kholia/HF-PA-v4/HF-PA-Simulations/5Vpp @ 5v @ 21 MHz.png

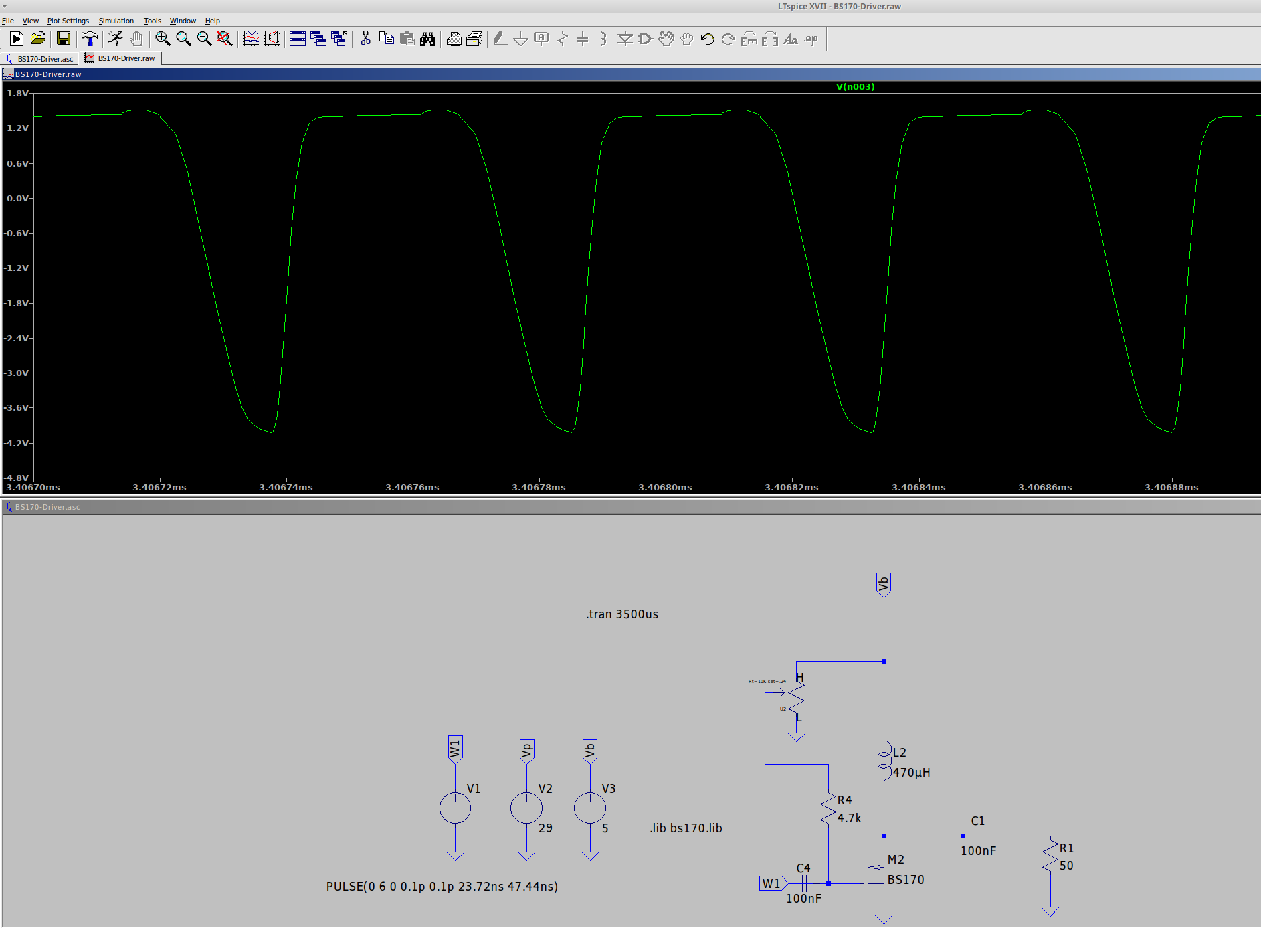
HF-PA-Simulations/5Vpp @ 5v @ 21 MHz.png
