kholia/HF-PA-v4/HF-PA-Simulations/8Vpp @ 5v.png

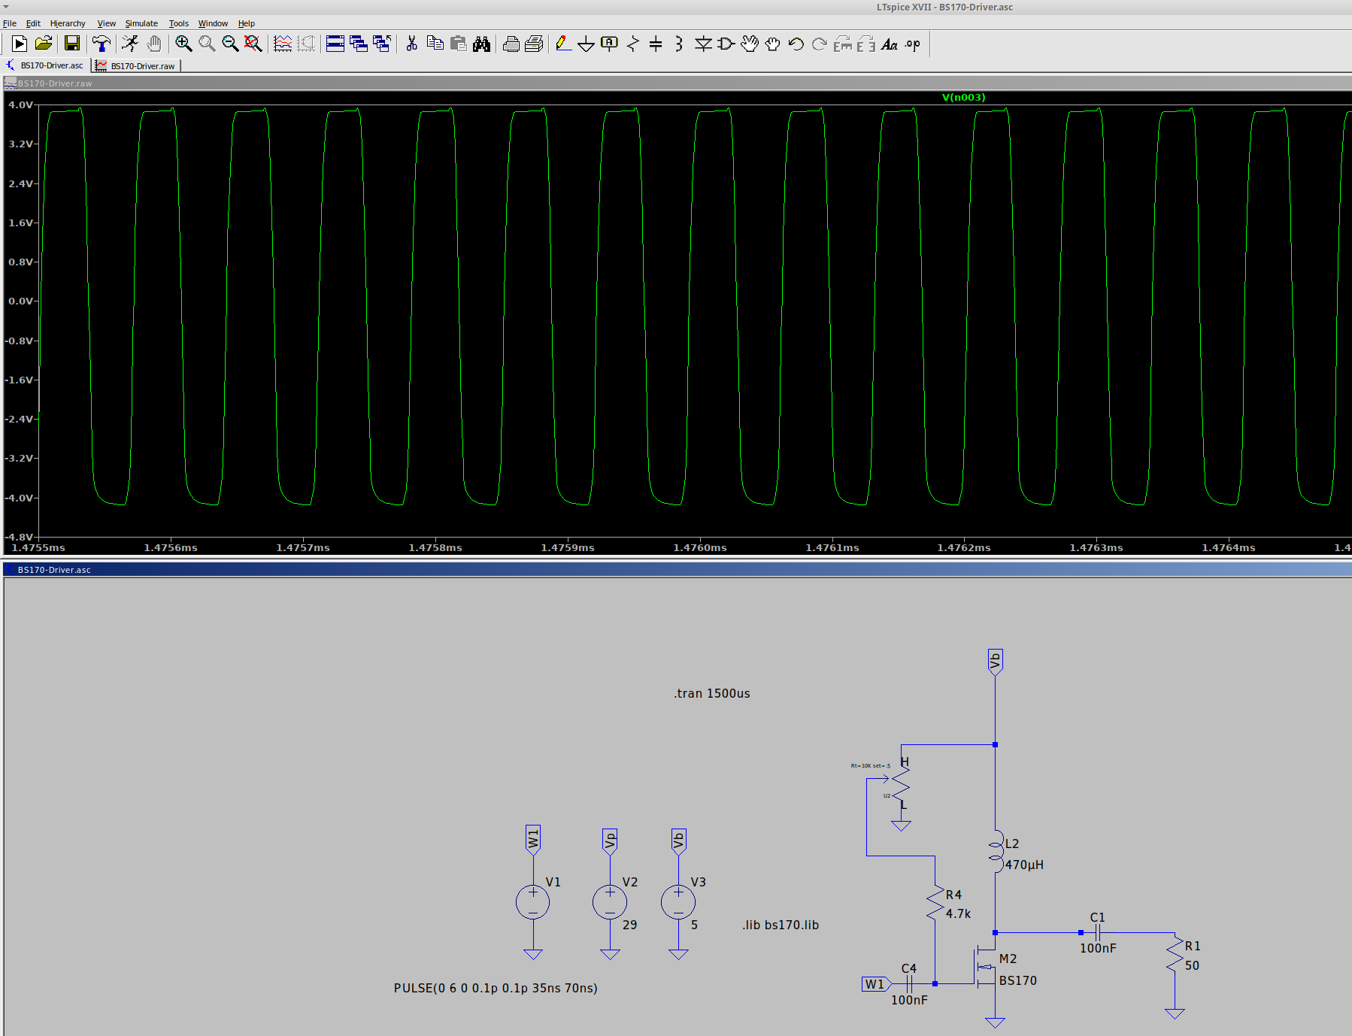
HF-PA-Simulations/8Vpp @ 5v.png
