kholia/HF-PA-v4/HF-PA-Simulations/11Vpp @ 9v @ 21 MHz.png

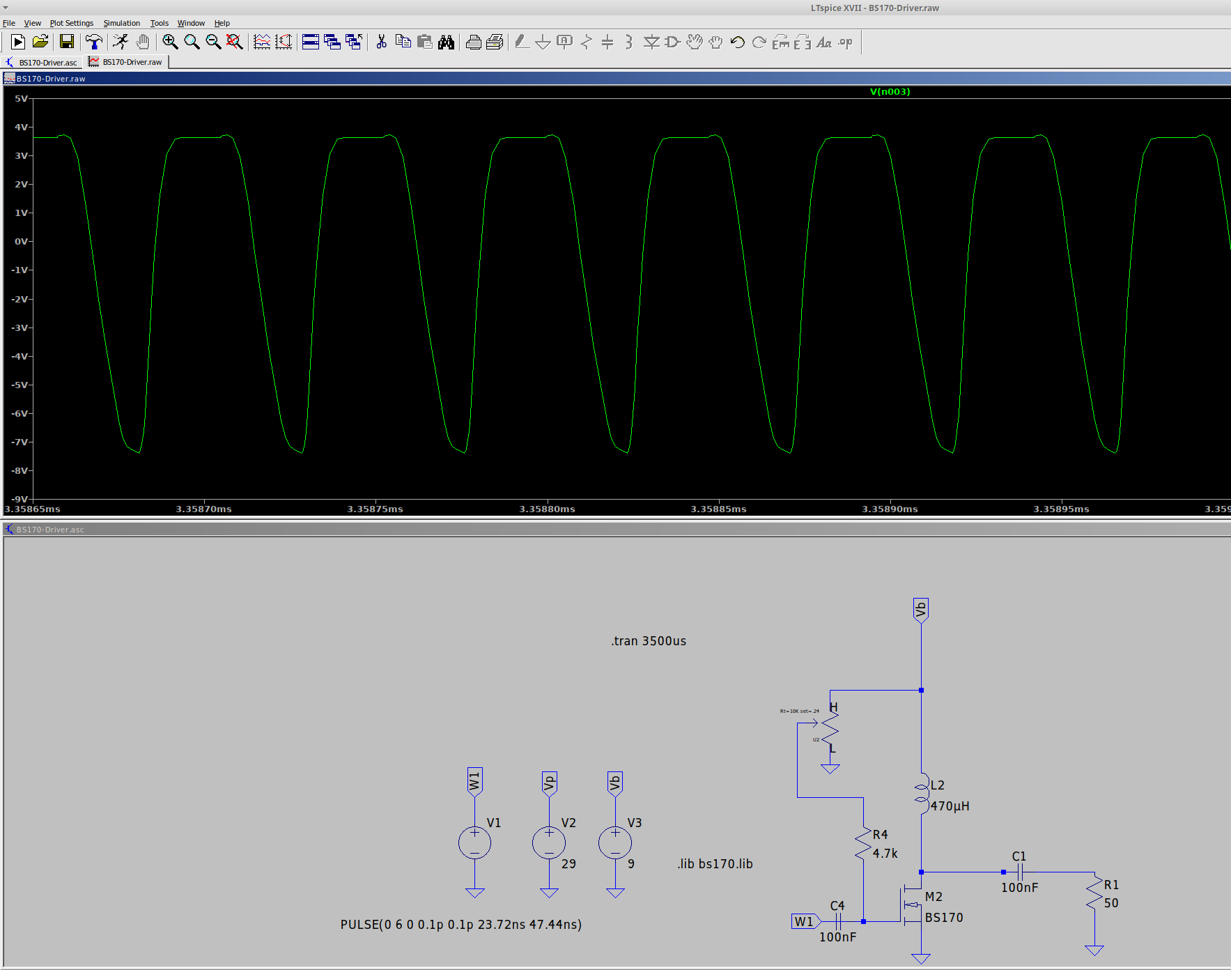
HF-PA-Simulations/11Vpp @ 9v @ 21 MHz.png
