kholia/HF-PA-v4/HF-PA-Simulations/12Vpp @ 9v.png

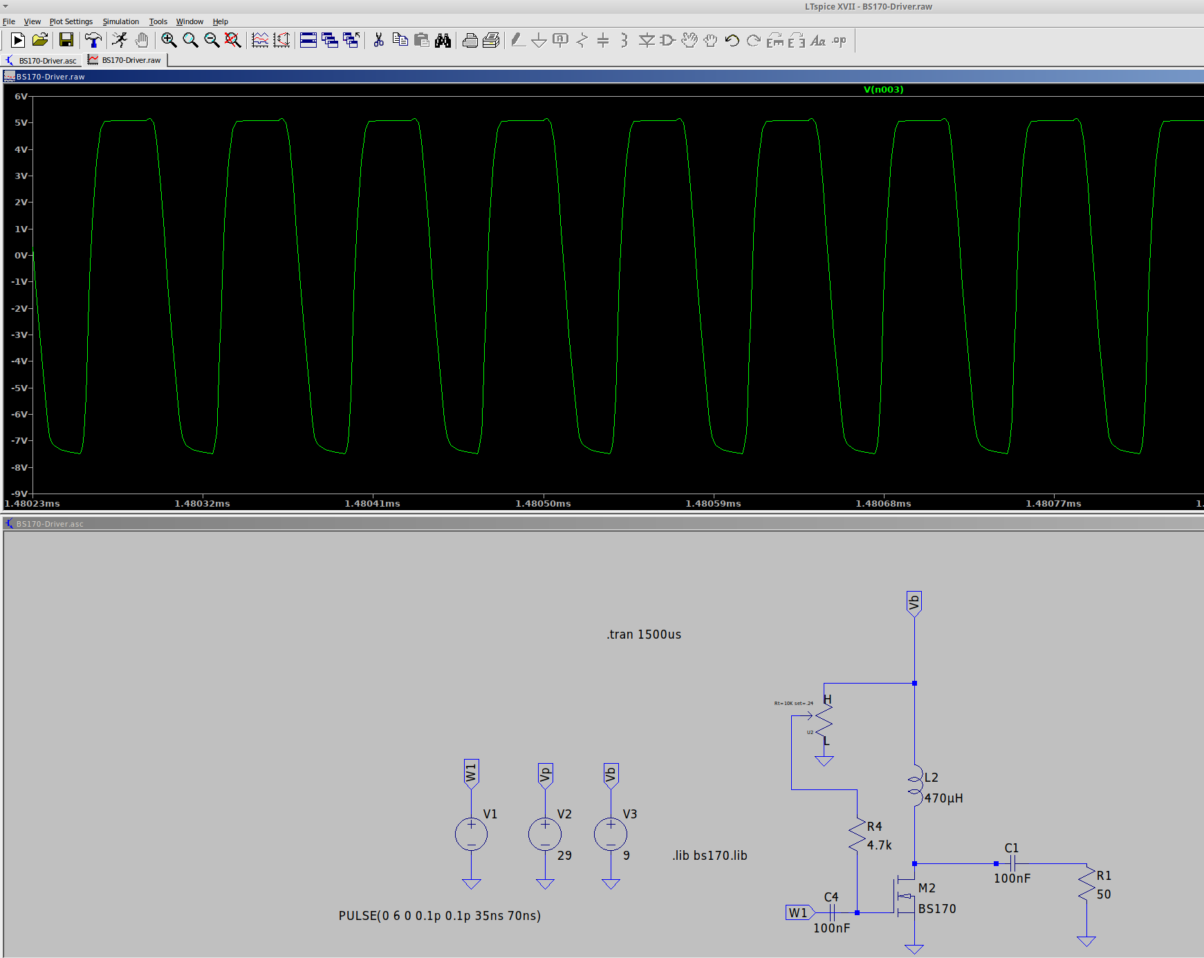
HF-PA-Simulations/12Vpp @ 9v.png
