kholia/HF-PA-v4/HF-PA-Simulations/12Vpp @ 12v @ 21 MHz (Actual Si5351 Drive).png

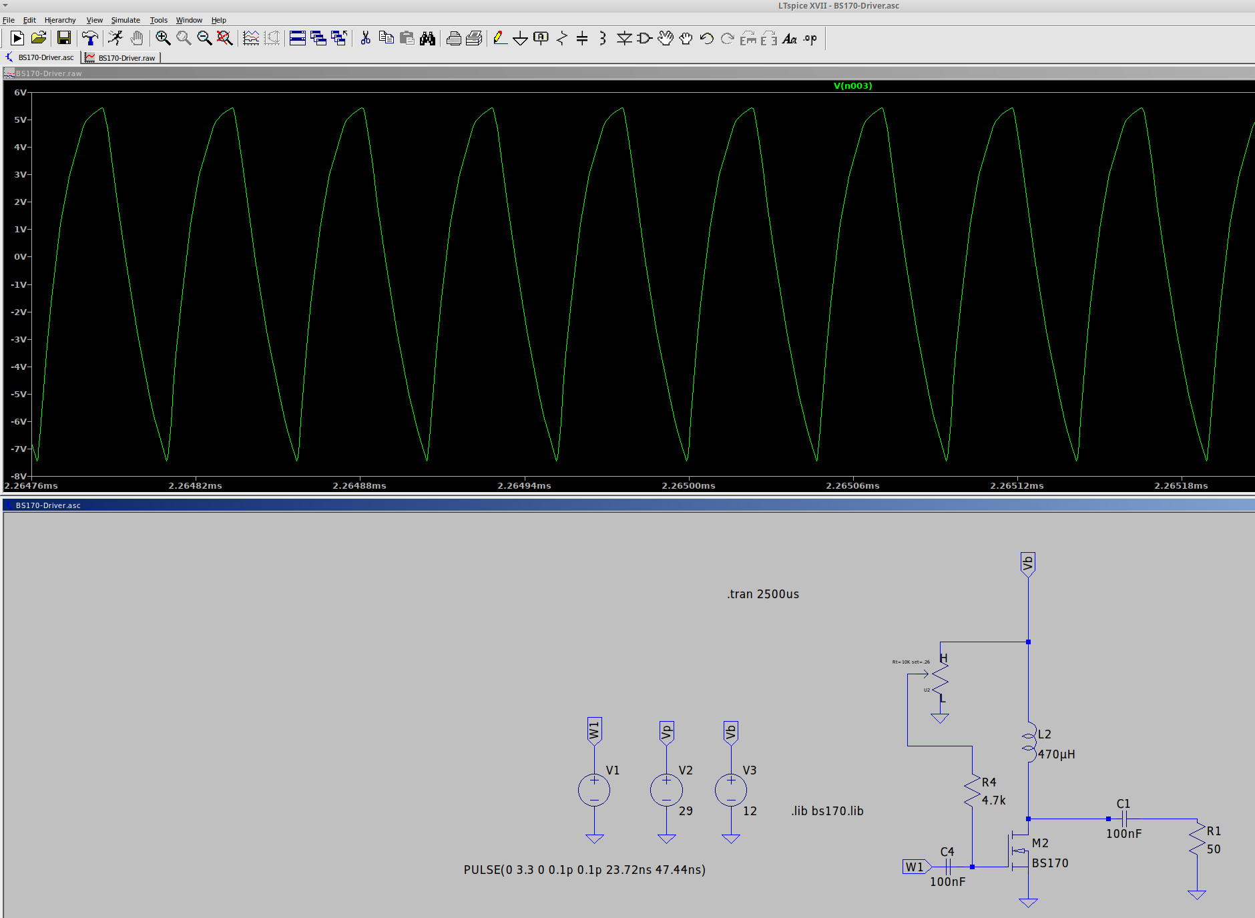
HF-PA-Simulations/12Vpp @ 12v @ 21 MHz (Actual Si5351 Drive).png
