kholia/HF-PA-v4/HF-PA-Simulations/17Vpp @ 12v @ 21 MHz.png

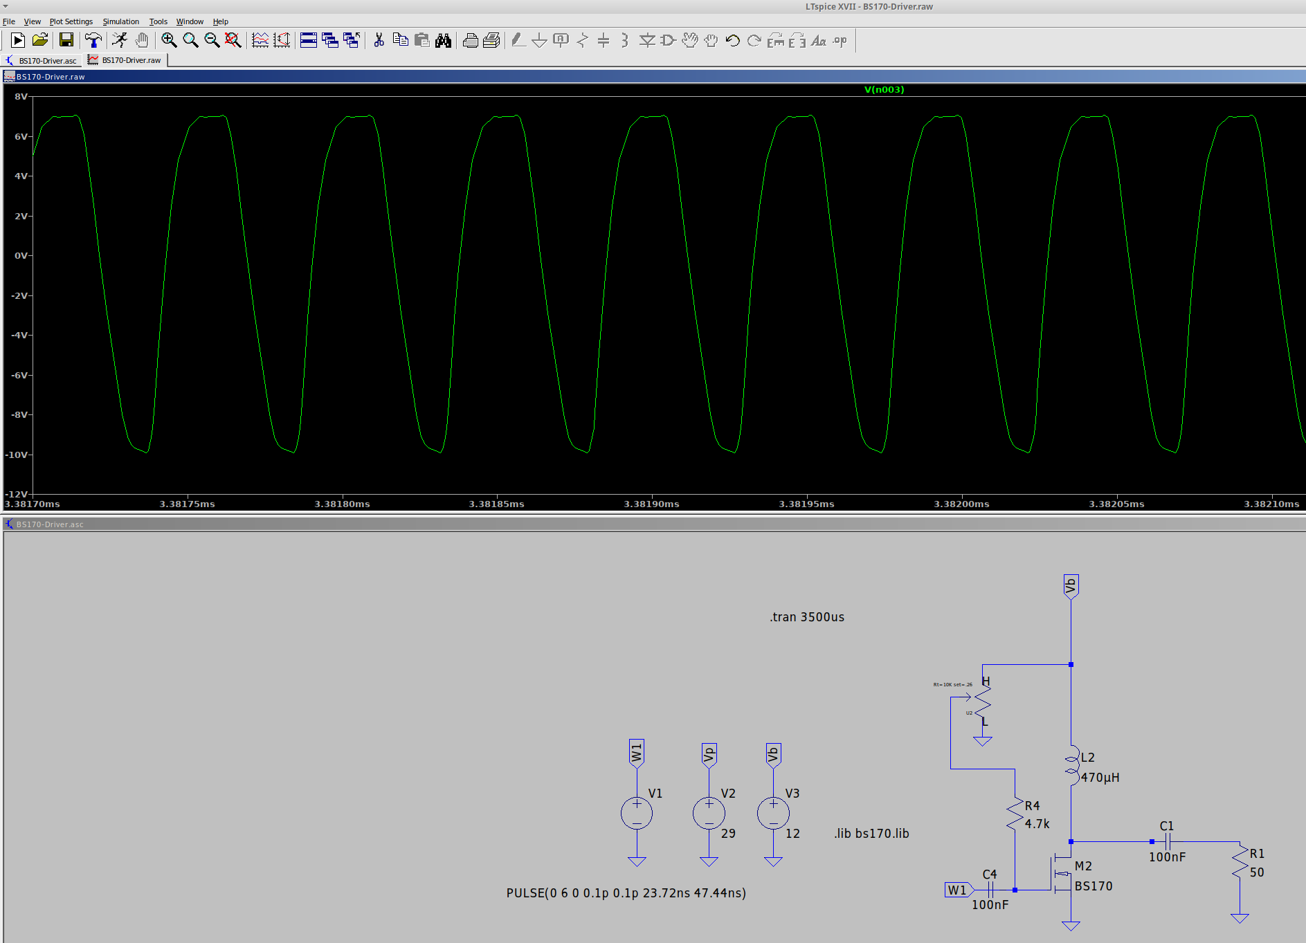
HF-PA-Simulations/17Vpp @ 12v @ 21 MHz.png
