kholia/HF-PA-v4/HF-PA-Simulations/DS1054Z_DS1ZA203916662_2021-10-18_14.36.06.png

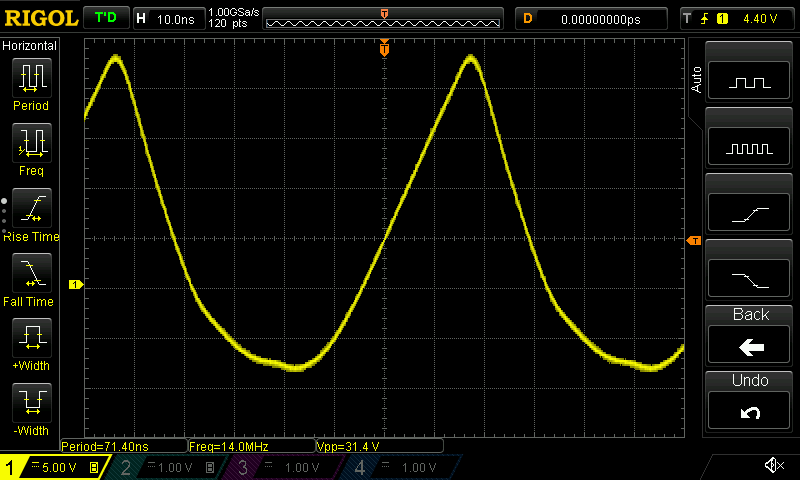
HF-PA-Simulations/DS1054Z_DS1ZA203916662_2021-10-18_14.36.06.png
