kholia/HF-PA-v4/HF-PA-Simulations/Screenshot_2021-10-14_11-42-27.png

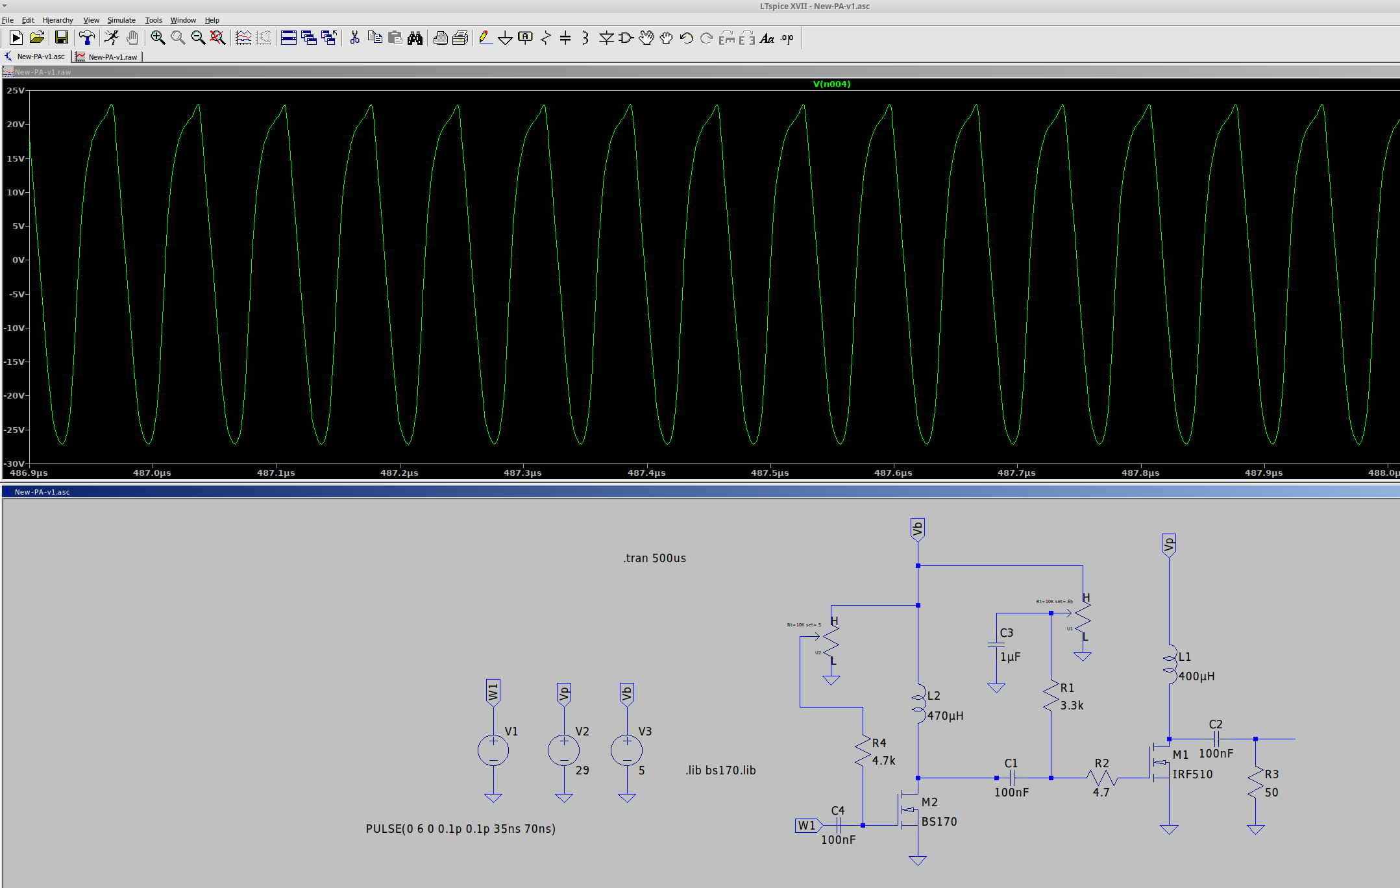
HF-PA-Simulations/Screenshot_2021-10-14_11-42-27.png
