kholia/HF-PA-v4/Info/25wlinear-small.png

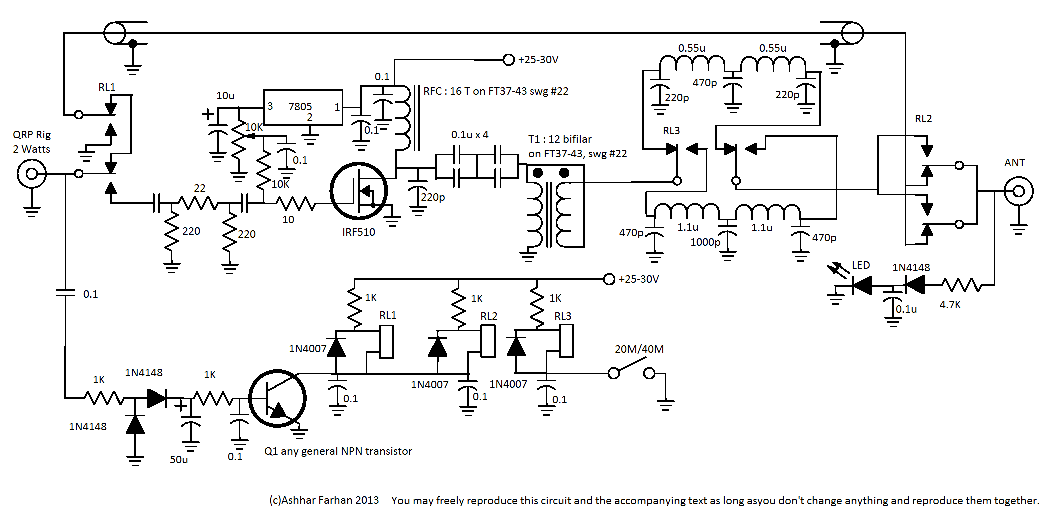
Info/25wlinear-small.png
