kholia/HF-PA-v4/Info/100nF 100V Non-Polar Polyester Film Capacitor - Philips.jpg

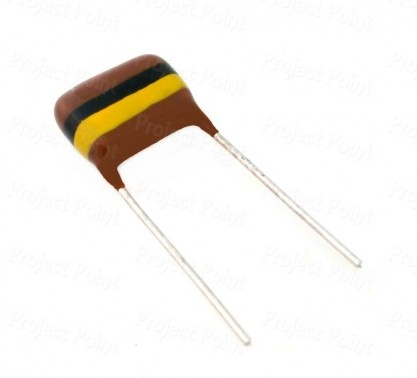
Info/100nF 100V Non-Polar Polyester Film Capacitor - Philips.jpg
