kholia/HF-PA-v4/Info/(220)_ZX-SSB_II_PA.png

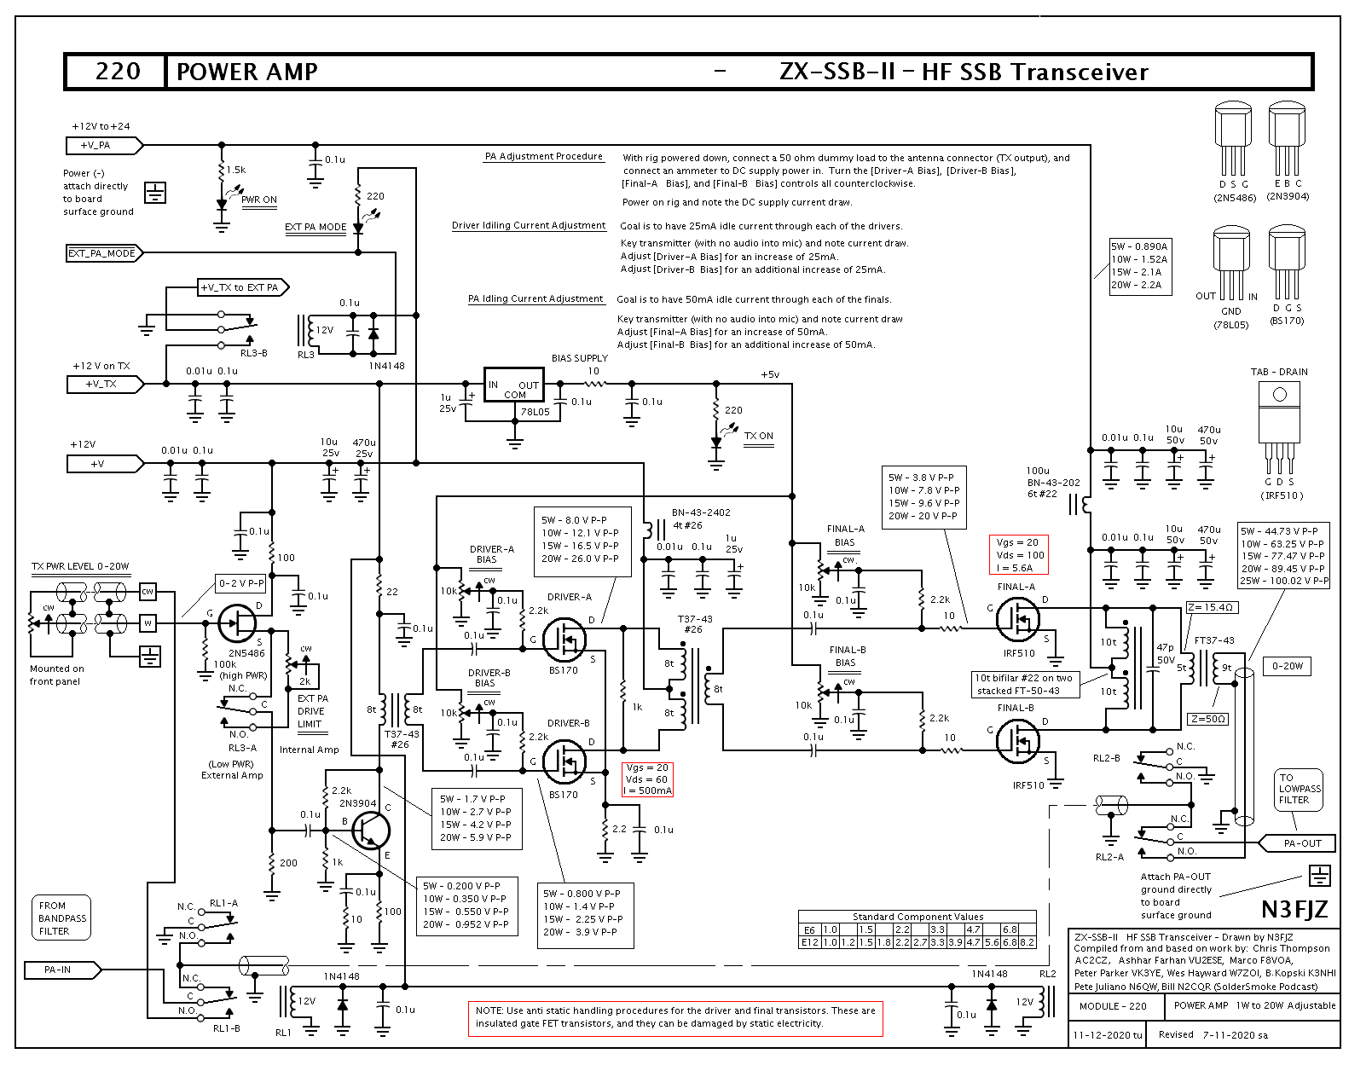
Info/(220)_ZX-SSB_II_PA.png
