kholia/HF-PA-v4/Info/Fake 7805 CV - Mar 2018.jpeg

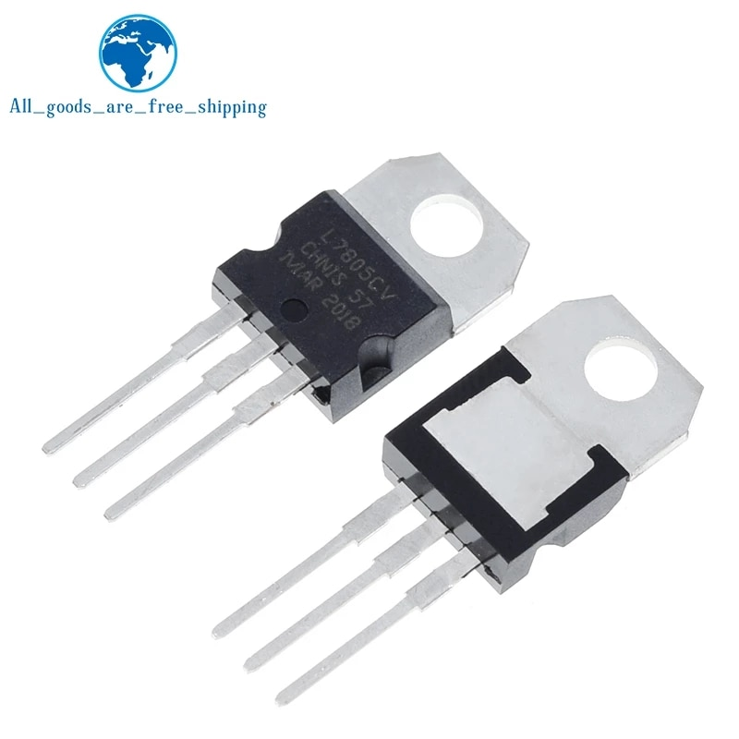
Info/Fake 7805 CV - Mar 2018.jpeg
