kholia/HF-PA-v4/Info/Fake ST 7805.jpg

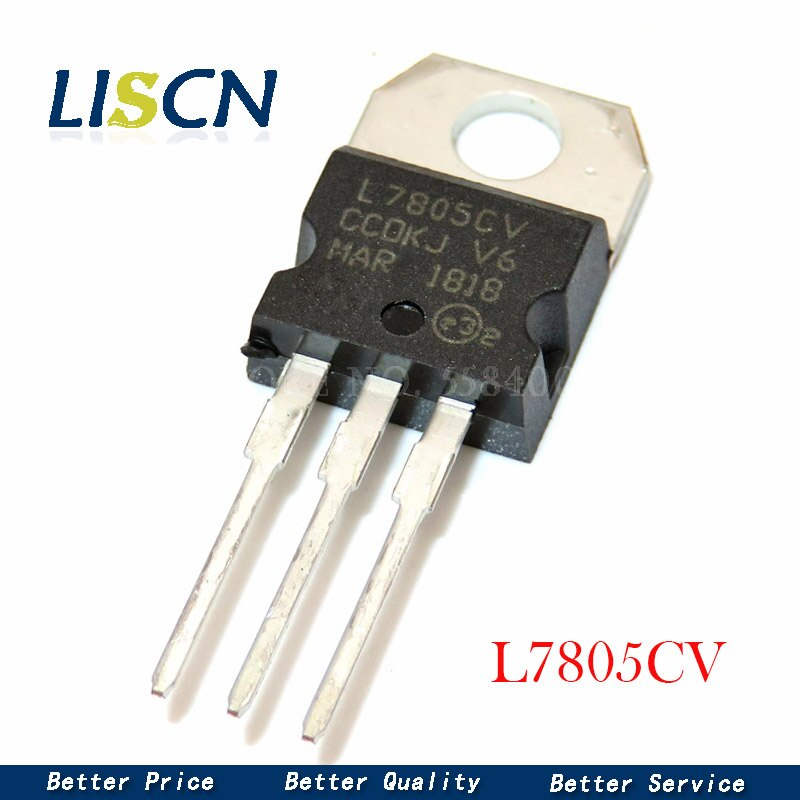
Info/Fake ST 7805.jpg
