kholia/HF-PA-v4/Info/Fake ST 7805.webp

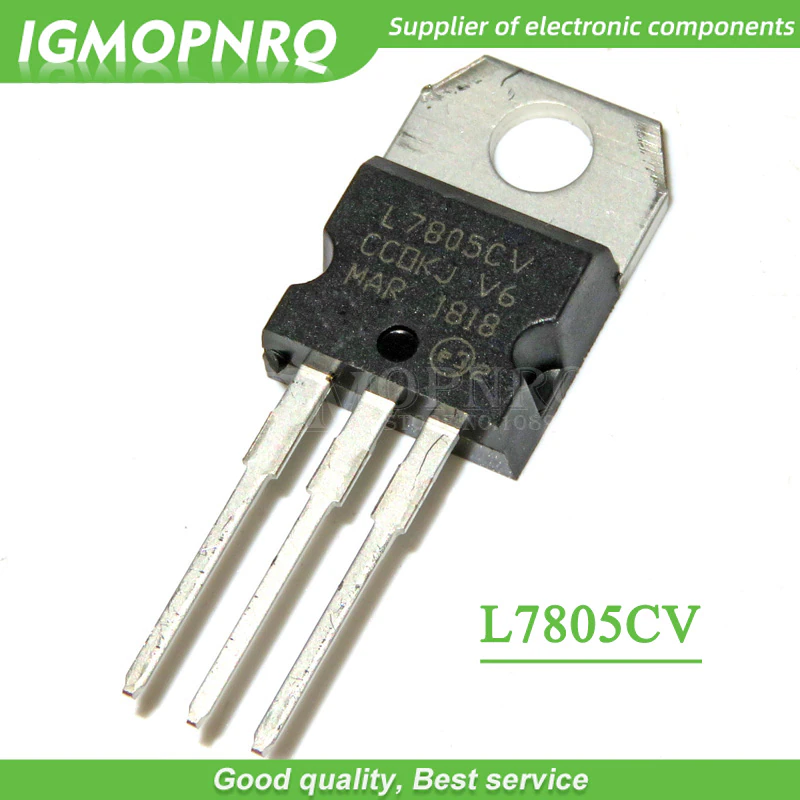
Info/Fake ST 7805.webp
