kholia/HF-PA-v4/Info/Heatsink TO-220.jpg

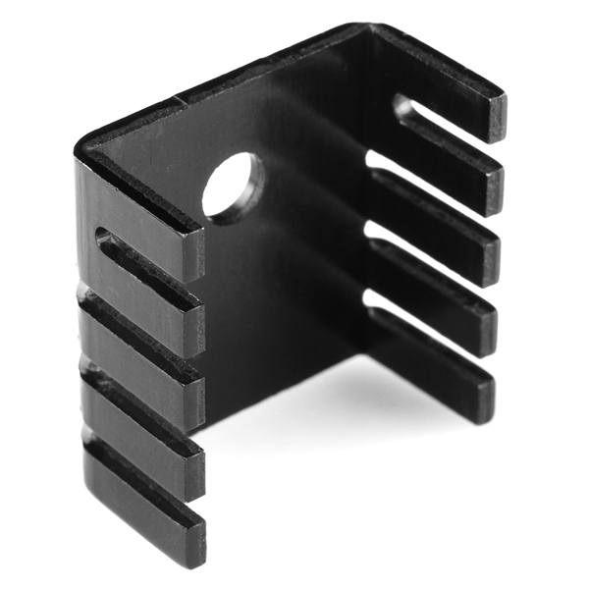
Info/Heatsink TO-220.jpg
