kholia/HF-PA-v4/Info/Hot mashup idea - was found independently on TG first.png

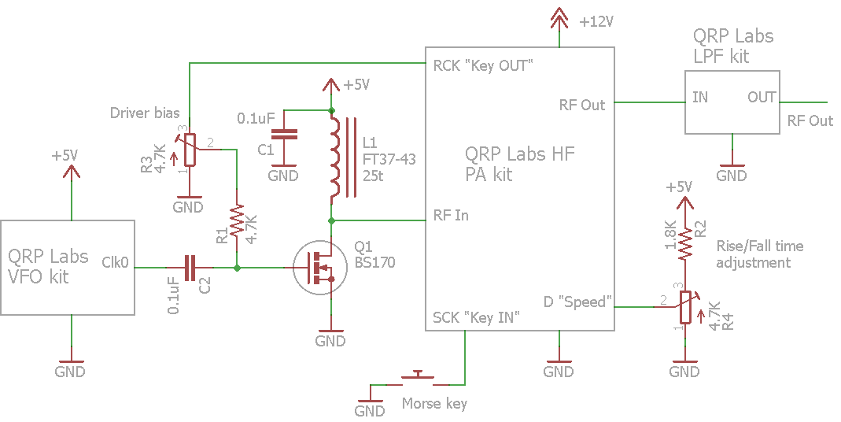
Info/Hot mashup idea - was found independently on TG first.png
