kholia/HF-PA-v4/Info/IRF530-SEC-TO-220.jpg

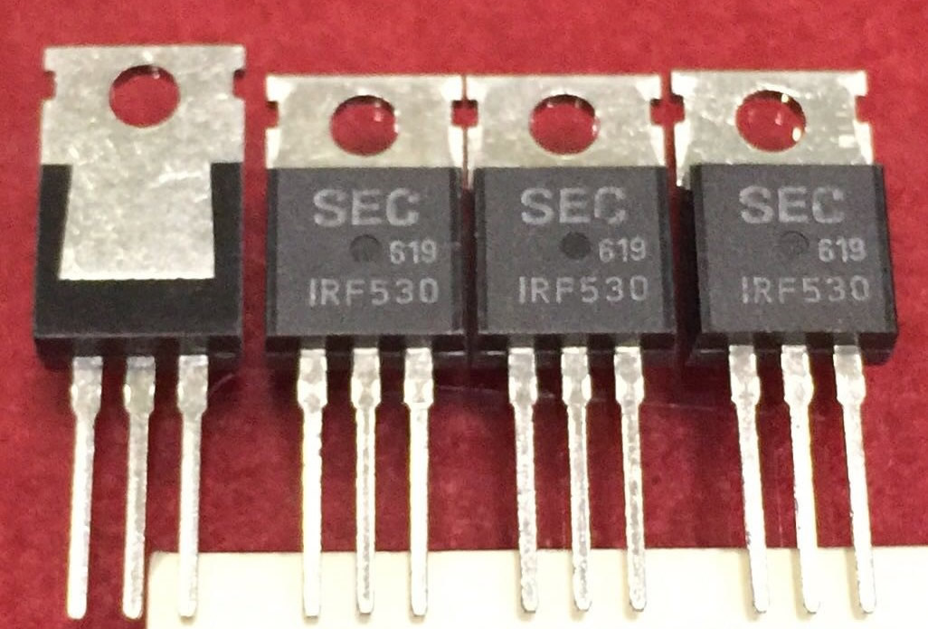
Info/IRF530-SEC-TO-220.jpg
