kholia/HF-PA-v4/Info/LM7805 Pinout.jpg

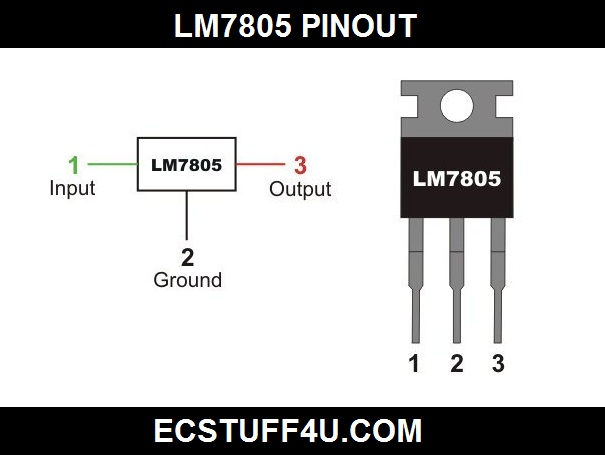
Info/LM7805 Pinout.jpg
