kholia/HF-PA-v4/Info/LPF_Values_Screenshot_2021-10-15_10-13-57.png

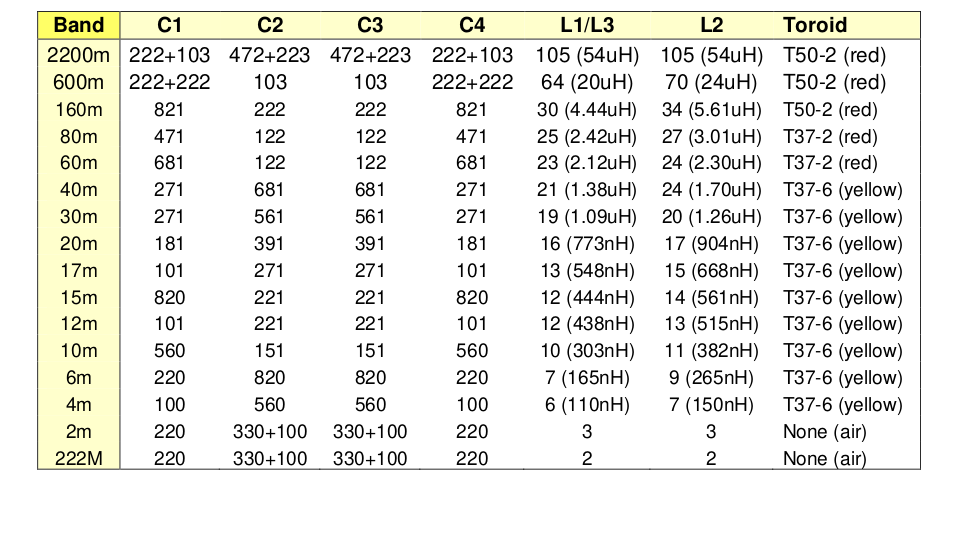
Info/LPF_Values_Screenshot_2021-10-15_10-13-57.png
