kholia/HF-PA-v4/Info/pa-1200x900.jpg

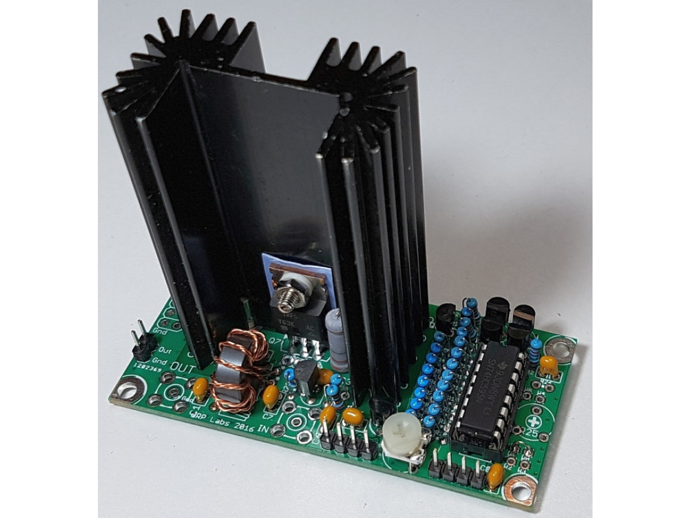
Info/pa-1200x900.jpg
