kholia/HF-PA-v4/Info/peanuts.GIF

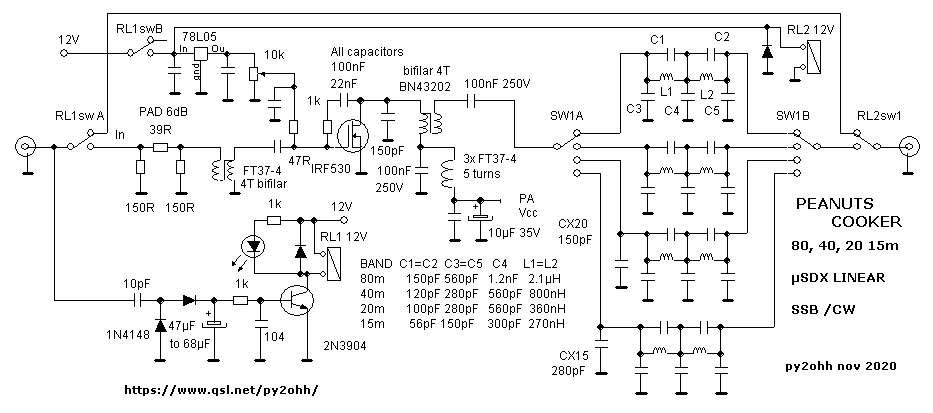
Info/peanuts.GIF
