kholia/HF-PA-v4/Info/PowerFreq1.gif

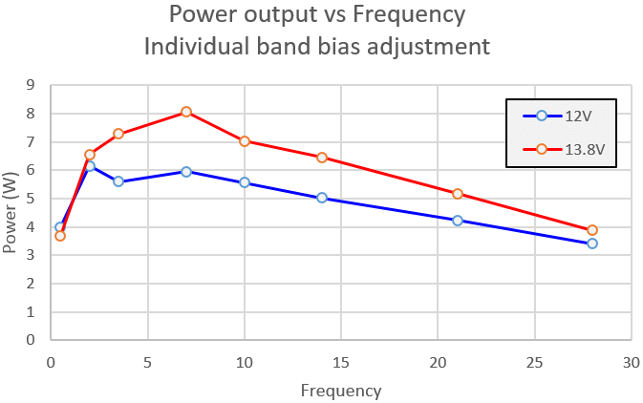
Info/PowerFreq1.gif
