kholia/HF-PA-v4/Info/PowerSupply1.gif

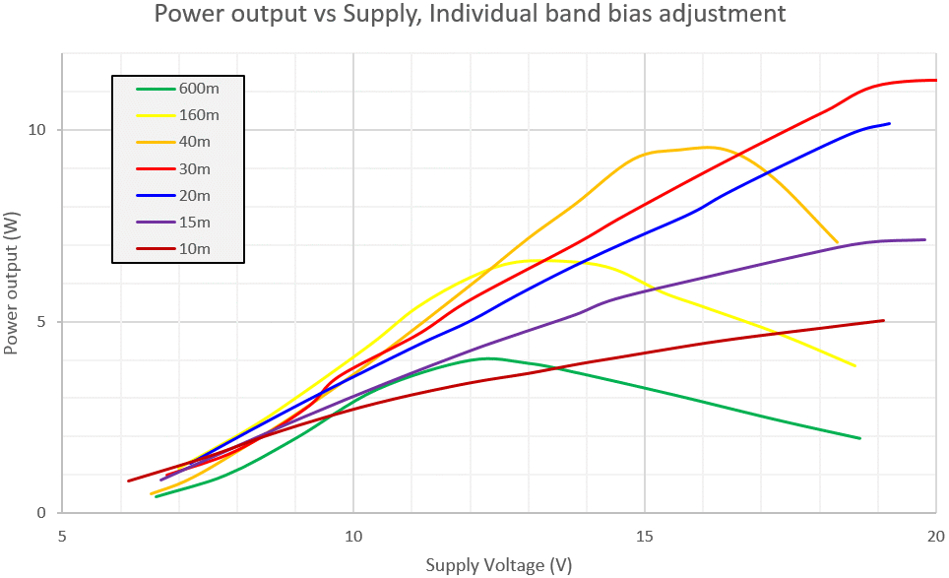
Info/PowerSupply1.gif
