kholia/HF-PA-v4/Info/QRP Labs HF PA 5W.png

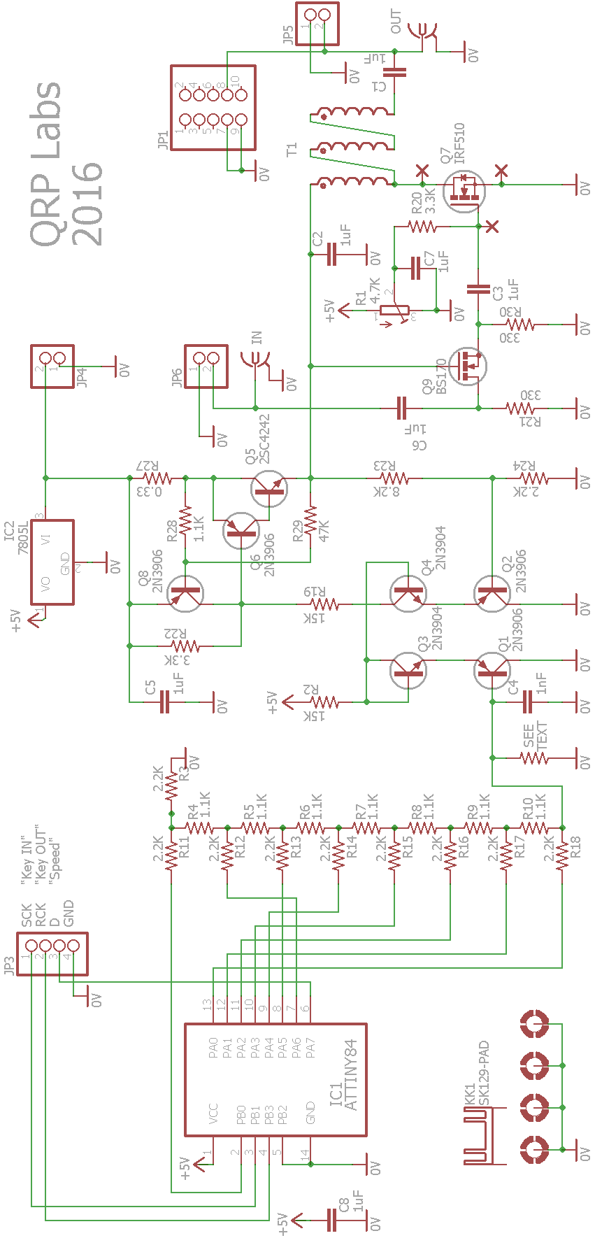
Info/QRP Labs HF PA 5W.png
