kholia/HF-PA-v4/Info/Recommended-PSU-2021-10-14-17.16.32.jpg

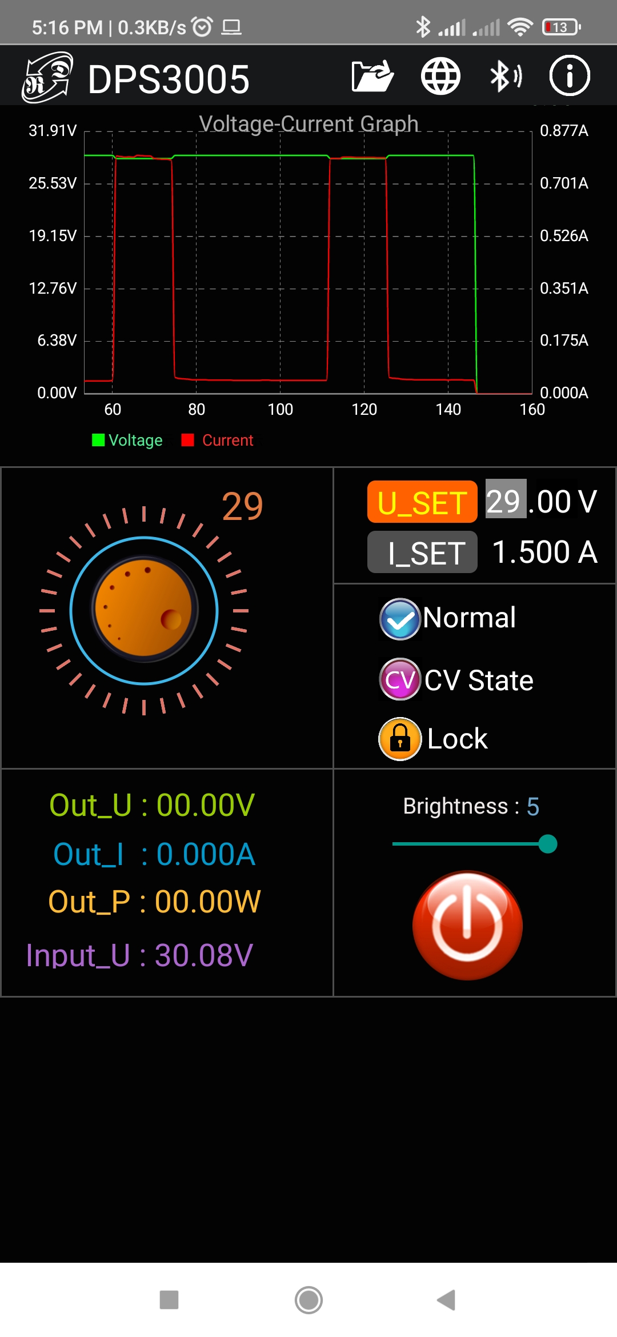
Info/Recommended-PSU-2021-10-14-17.16.32.jpg
