kholia/HF-PA-v4/Info/RM065-672x378.jpg

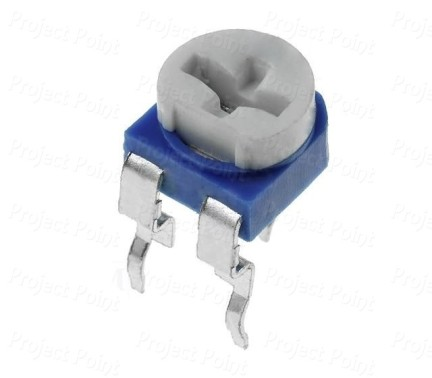
Info/RM065-672x378.jpg
