kholia/HF-PA-v4/Info/Screenshot_2021-09-23_19-27-11.png

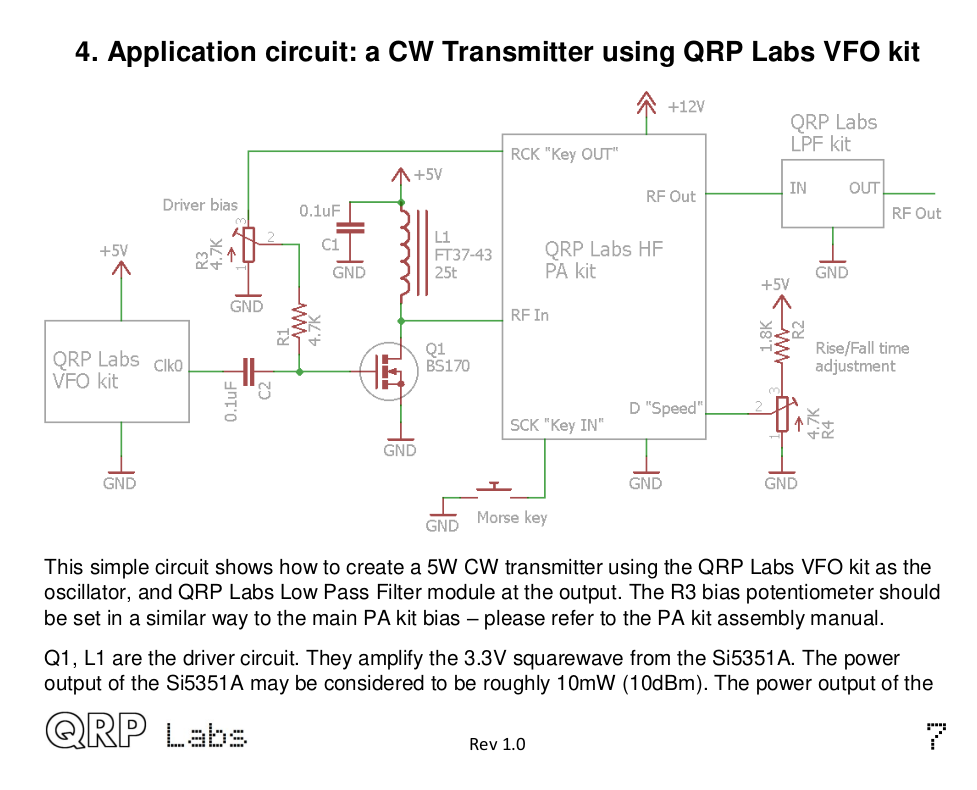
Info/Screenshot_2021-09-23_19-27-11.png
