kholia/HF-PA-v4/Info/Screenshot_2021-10-14_07-44-31.png

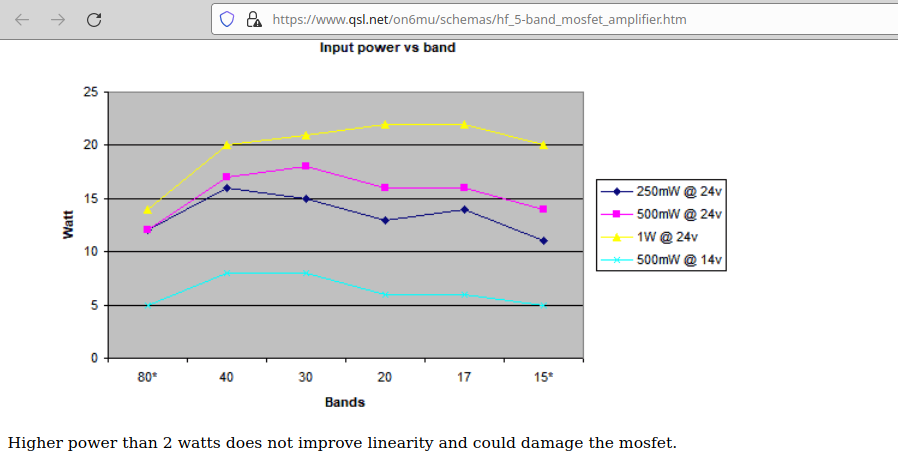
Info/Screenshot_2021-10-14_07-44-31.png
