kholia/HF-PA-v4/Info/Stability-2-ARRL-Chapter-17-2019.png

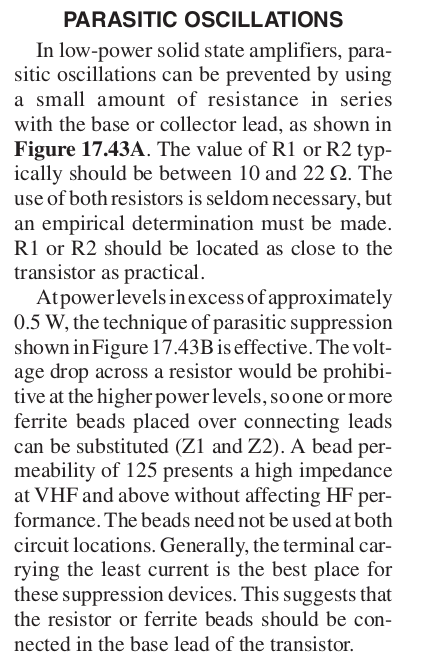
Info/Stability-2-ARRL-Chapter-17-2019.png
