kholia/HF-PA-v4/Info/VU2ESE-Linear-20131122_081706.jpg

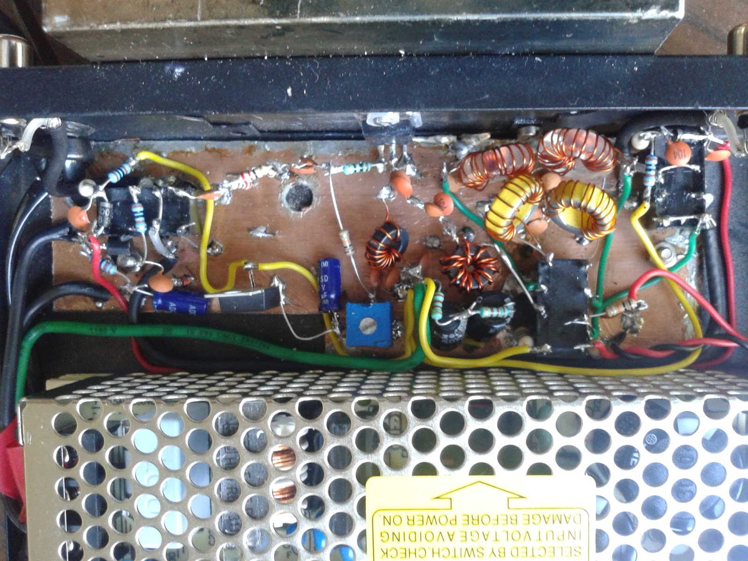
Info/VU2ESE-Linear-20131122_081706.jpg
