kholia/HF-PA-v4/LPF-Screenshot_2021-07-15_11-28-38.png

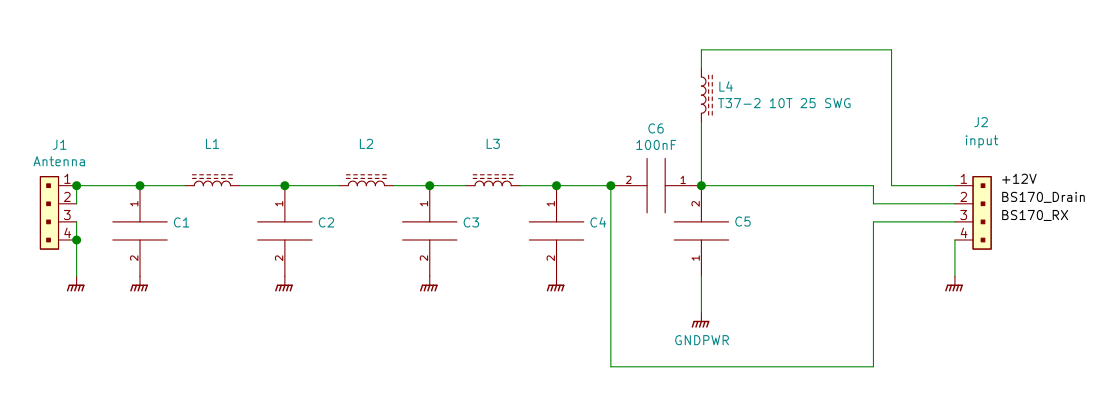
LPF-Screenshot_2021-07-15_11-28-38.png
