kholia/HF-PA-v4/LPF_Screenshot_2021-10-15_10-15-40.png

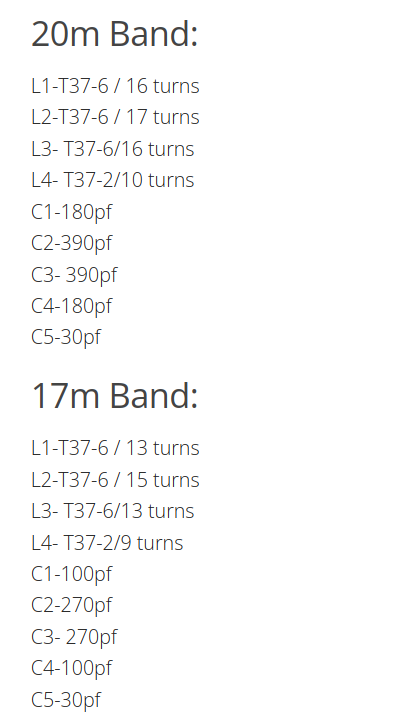
LPF_Screenshot_2021-10-15_10-15-40.png
