kholia/HF-PA-v4/PA-v4.1.png

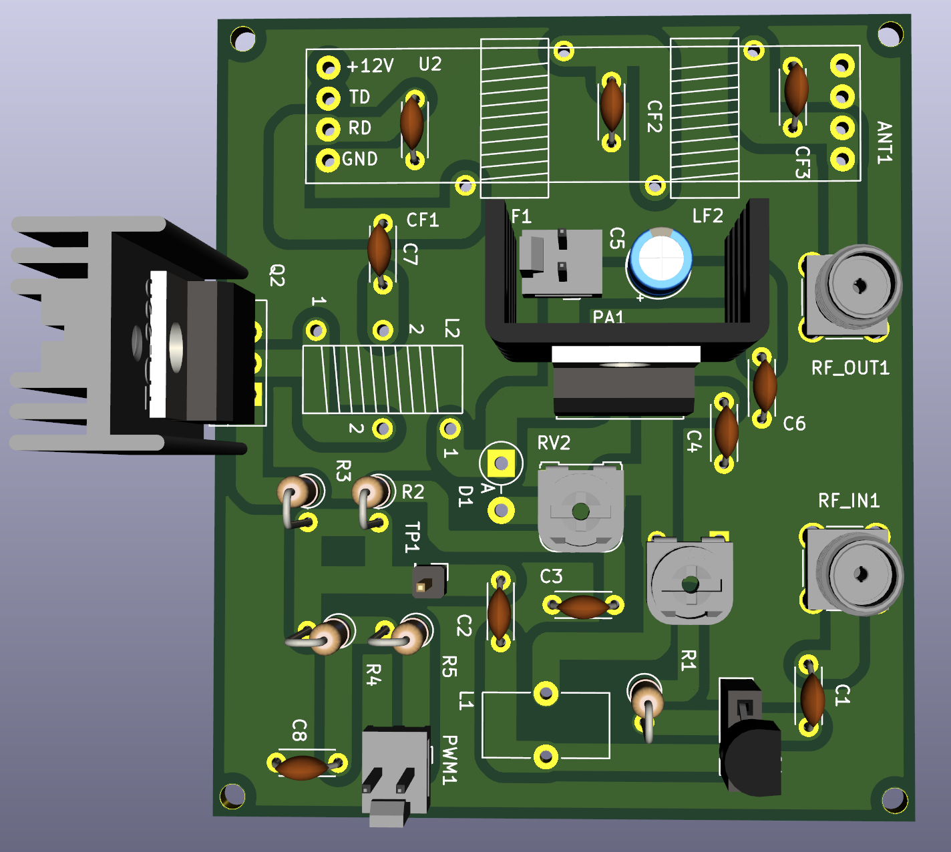
PA-v4.1.png
