kholia/HF-PA-v4/PA-v4.3.png

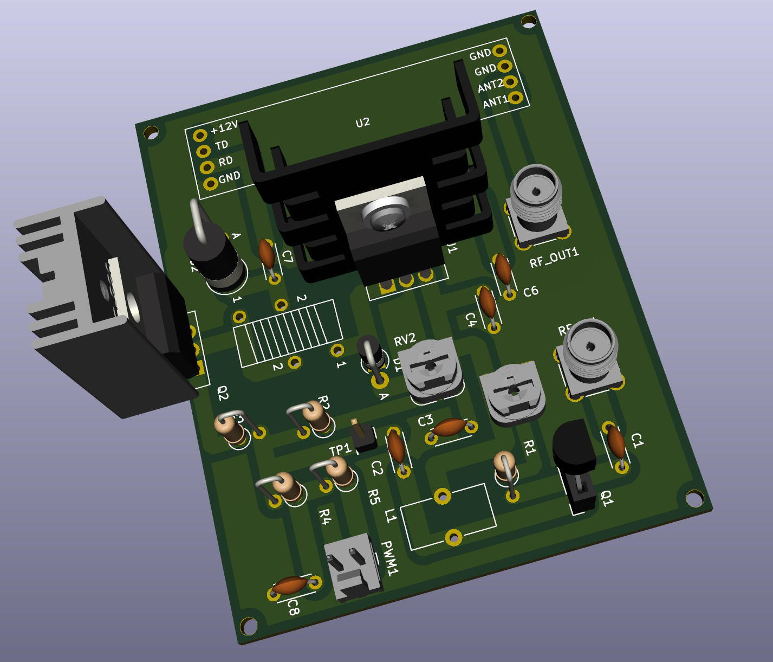
PA-v4.3.png
