kholia/HF-PA-v4/RX-Reports/Screenshot_2021-10-18_16-47-04.png

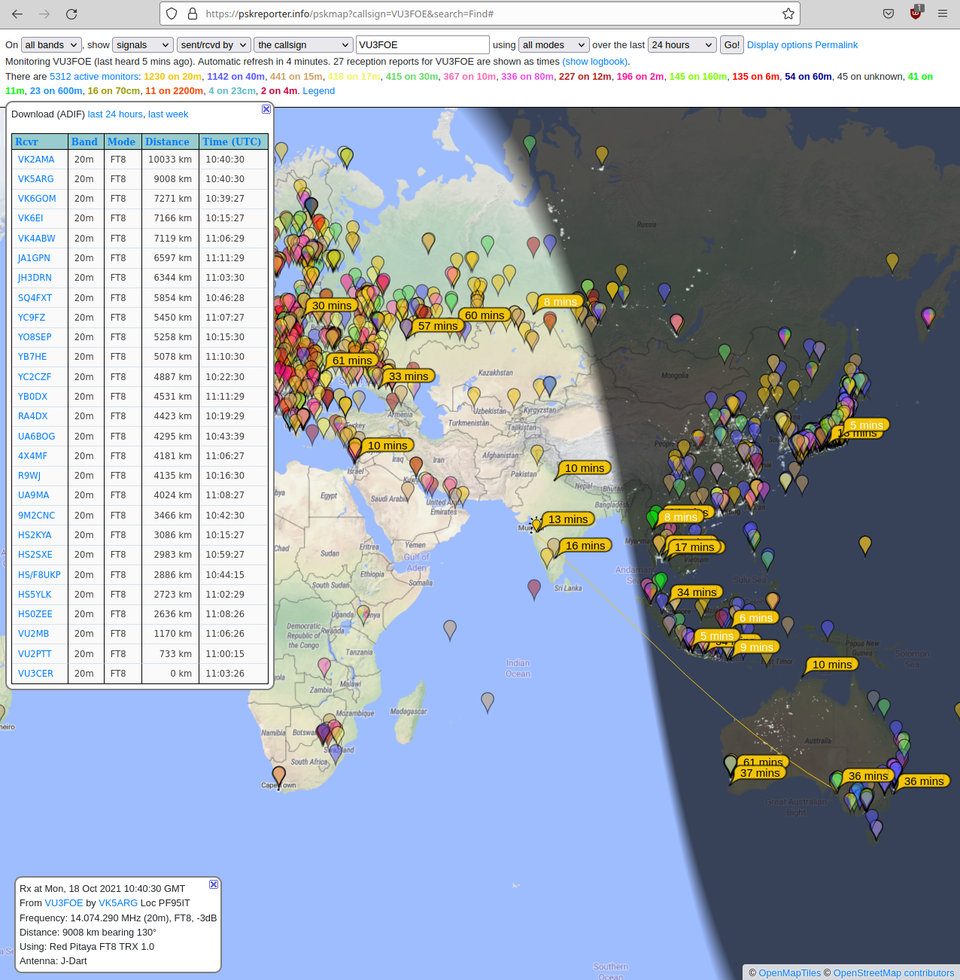
RX-Reports/Screenshot_2021-10-18_16-47-04.png
