kholia/HF-PA-v4/RX-Reports/Screenshot_2021-10-19_17-20-36.png

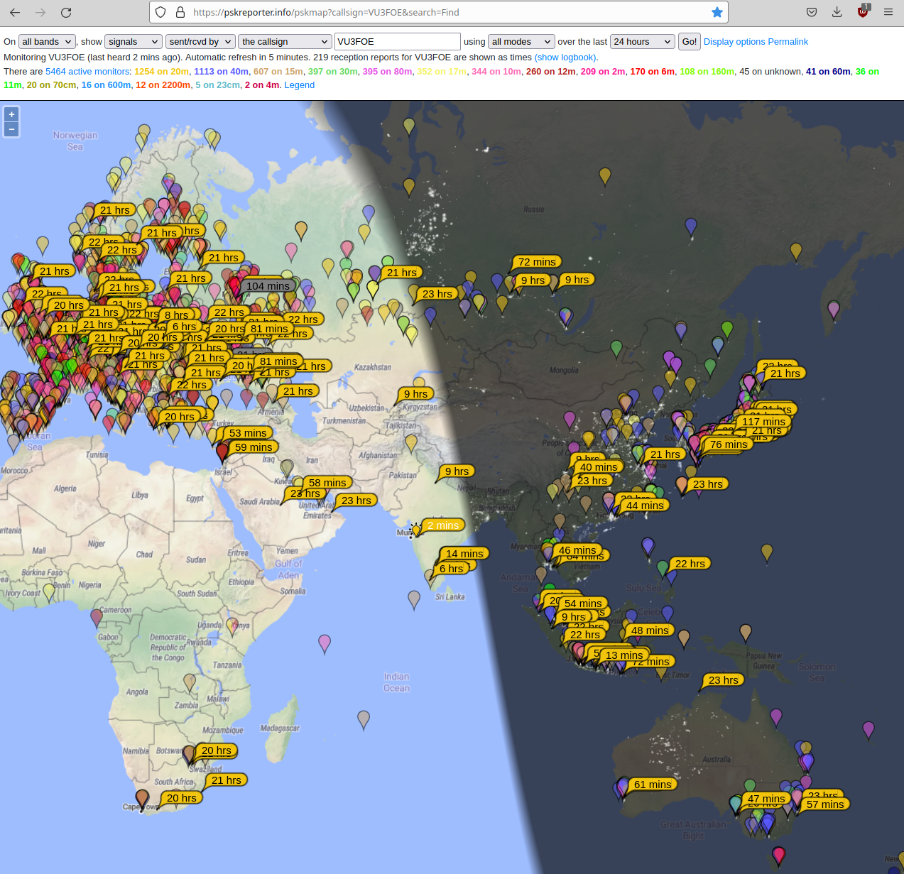
RX-Reports/Screenshot_2021-10-19_17-20-36.png
