kholia/HF-PA-v4/RX-Reports/TX-v4.3-Screenshot_2021-11-06_08-04-19.png

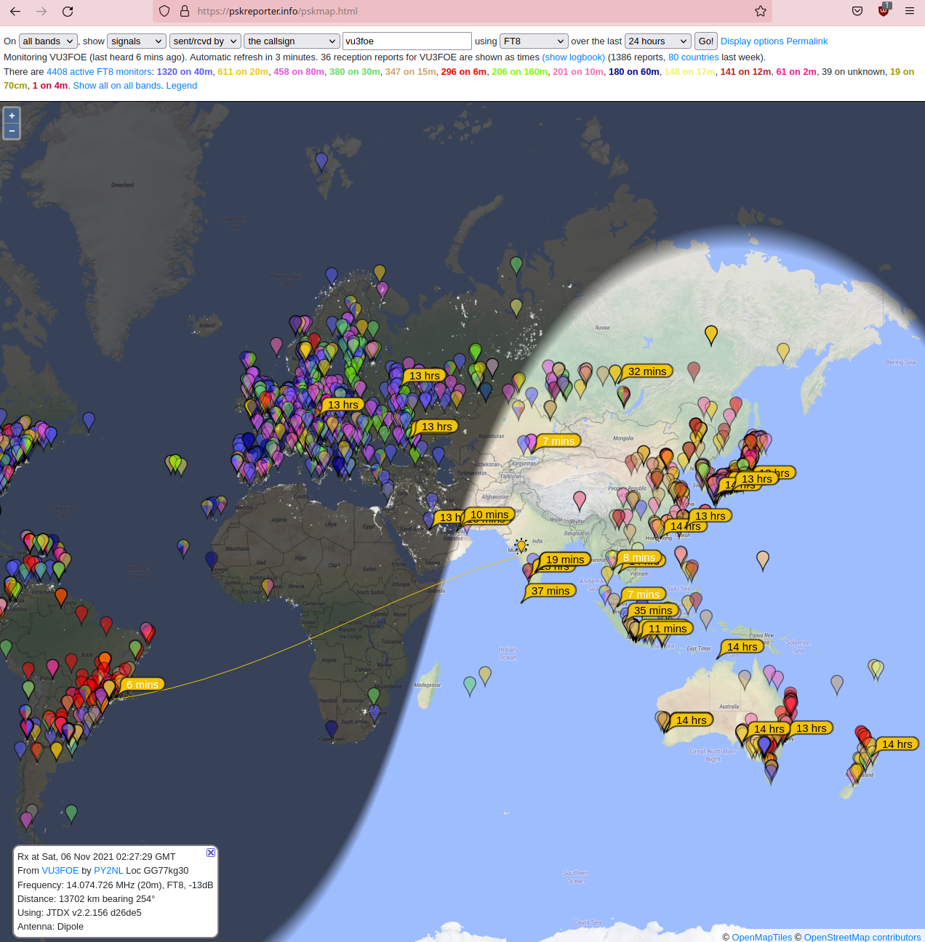
RX-Reports/TX-v4.3-Screenshot_2021-11-06_08-04-19.png
