kholia/HF-PA-v4/RX-Reports/TX-v4.3-Screenshot_2021-11-06_21-49-38.png

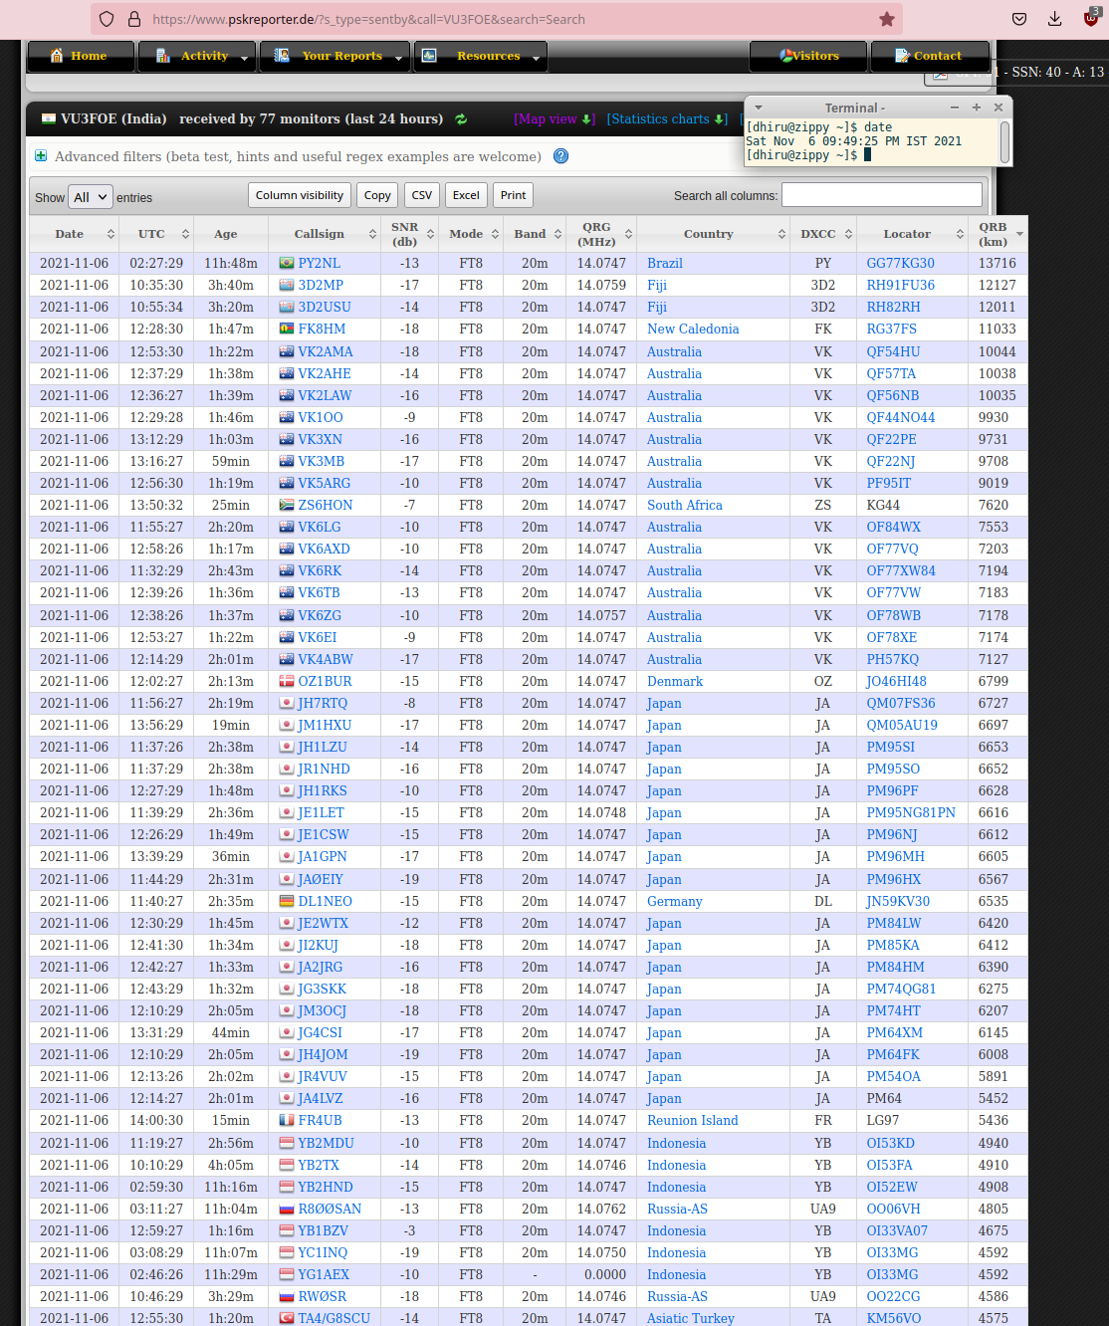
RX-Reports/TX-v4.3-Screenshot_2021-11-06_21-49-38.png
