kholia/HF-PA-v4/Wider-LPF/F1.png

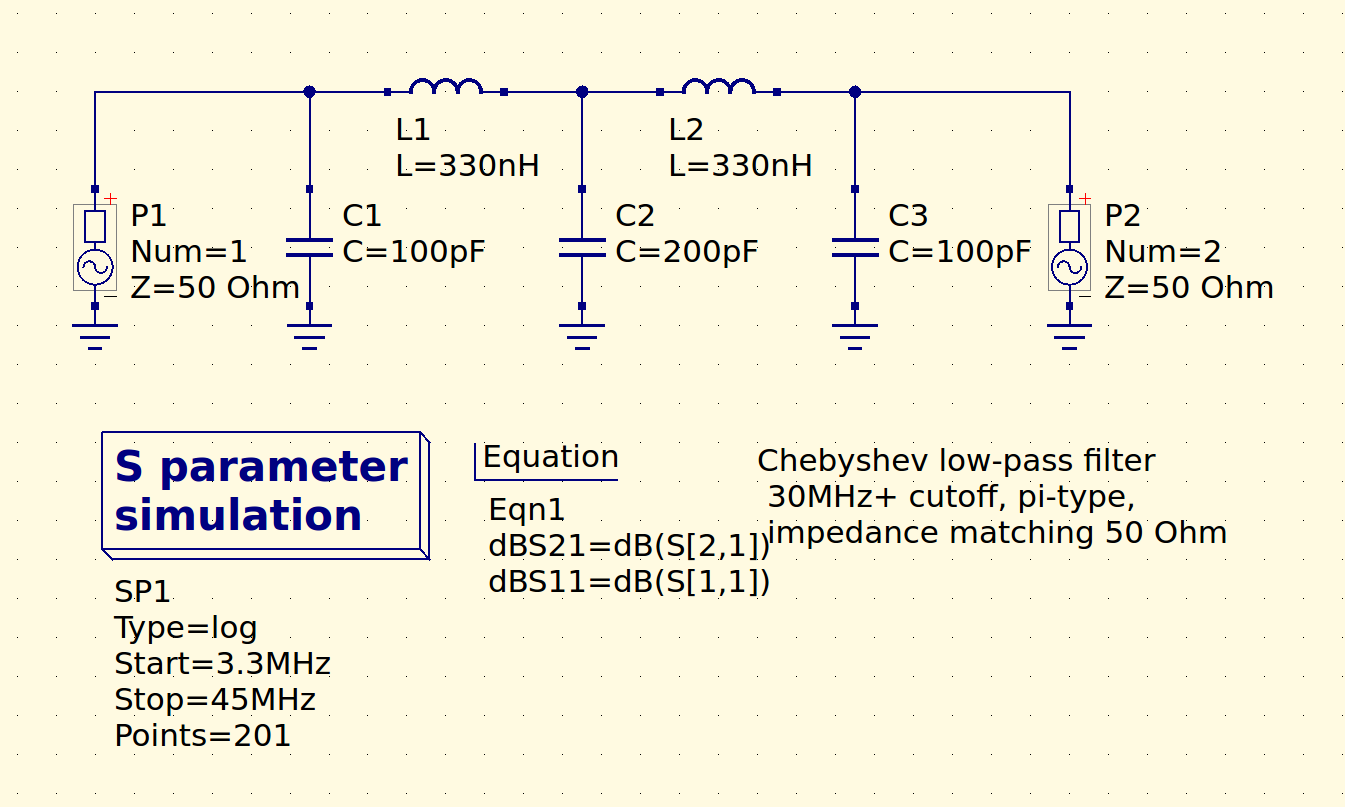
Wider-LPF/F1.png
