kholia/HF-PA-v4/Wider-LPF/F2.png

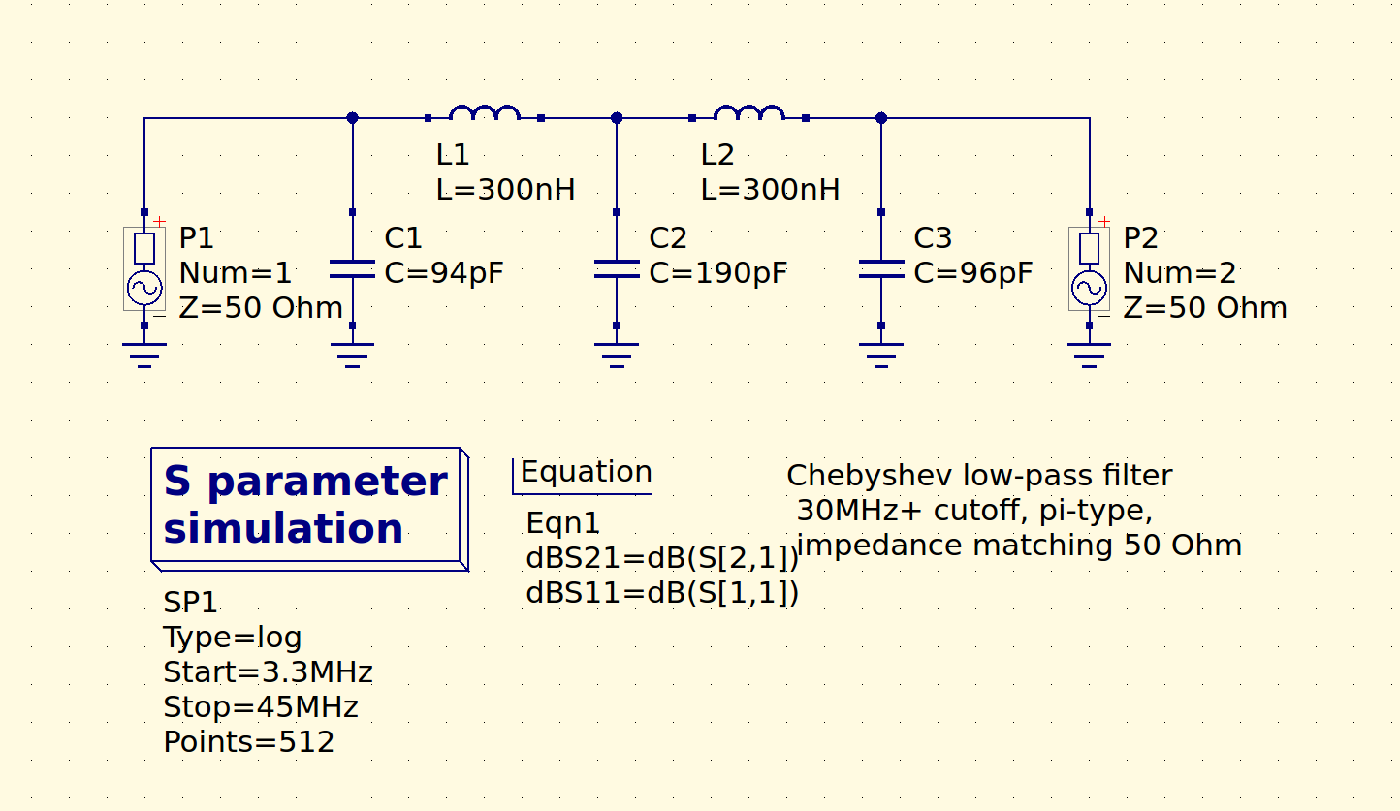
Wider-LPF/F2.png
