kholia/HF-PA-v4/Wider-LPF/LPF-Schematic.png

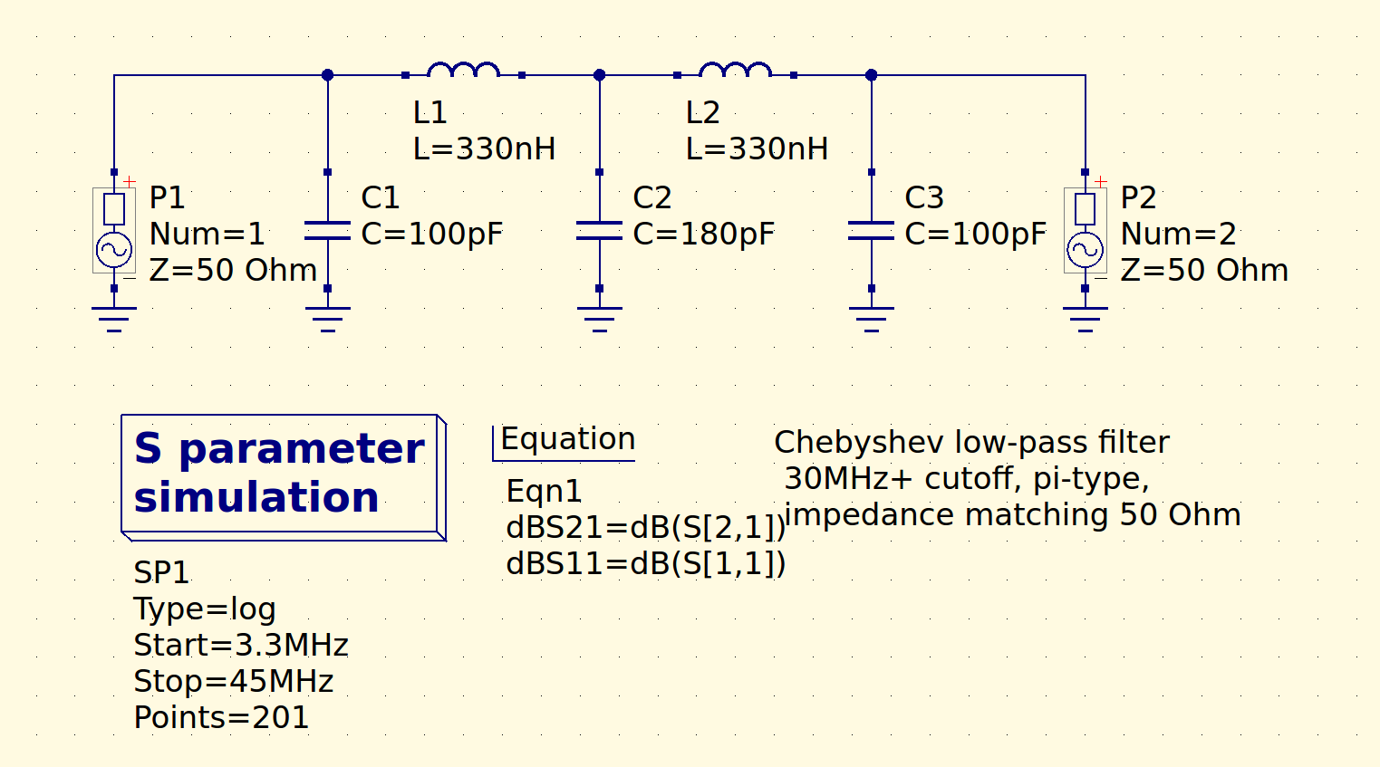
Wider-LPF/LPF-Schematic.png
