kholia/HF-PA-v4/Wider-LPF/Screenshot_2021-10-15_14-21-57.png

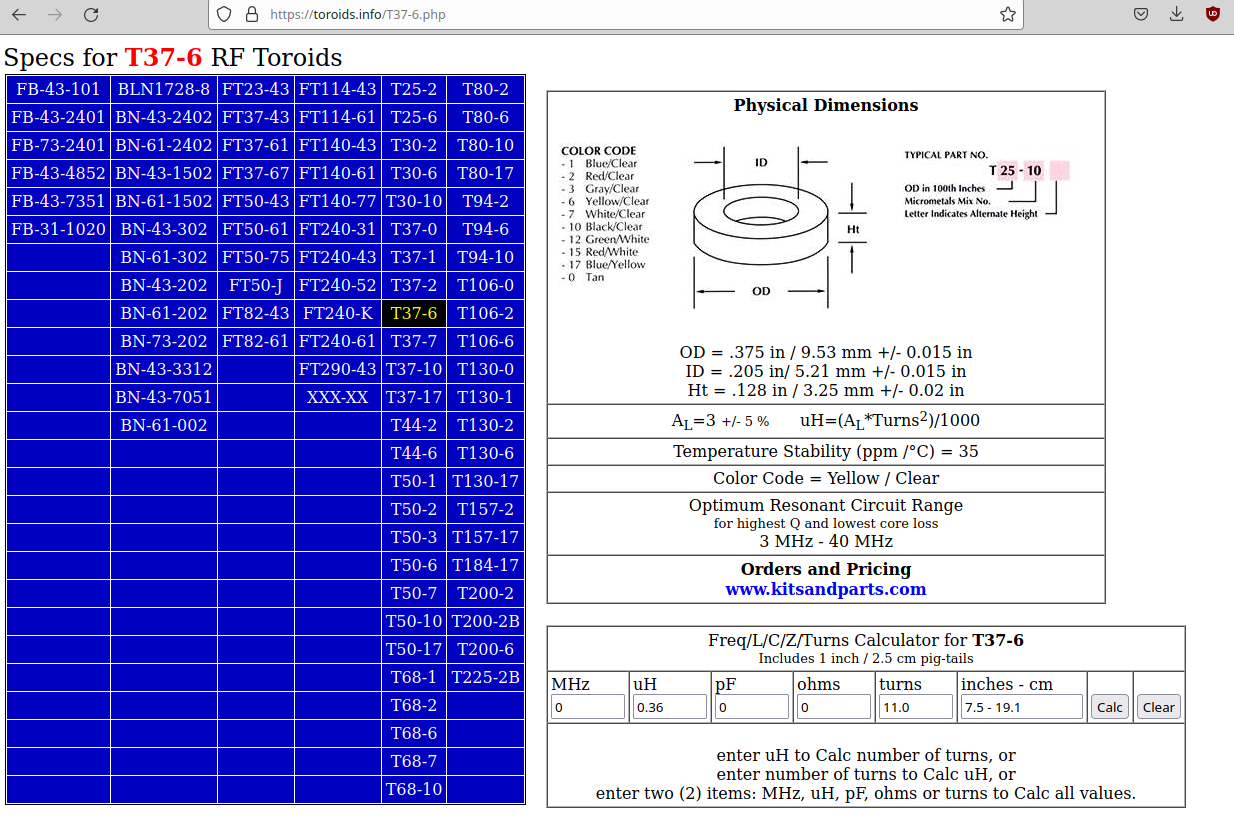
Wider-LPF/Screenshot_2021-10-15_14-21-57.png
