kholia/HF-PA-v4/Wider-LPF/Screenshot_2021-10-17_13-45-53.png

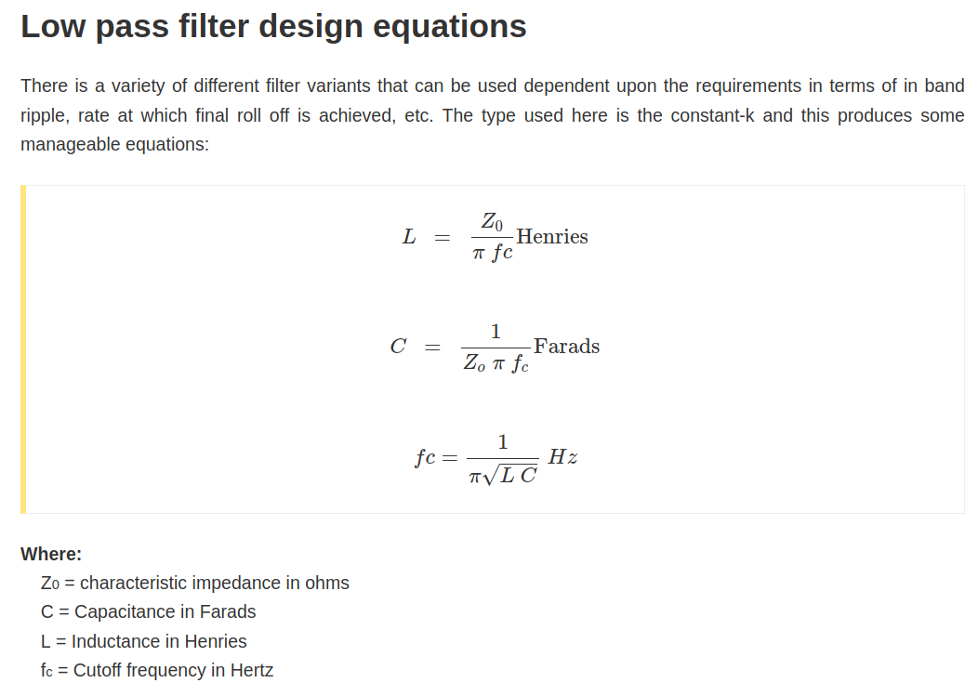
Wider-LPF/Screenshot_2021-10-17_13-45-53.png
