kholia/HF-PA-v4/Info/Cost is RM 0.50 - Fake or real.jpeg

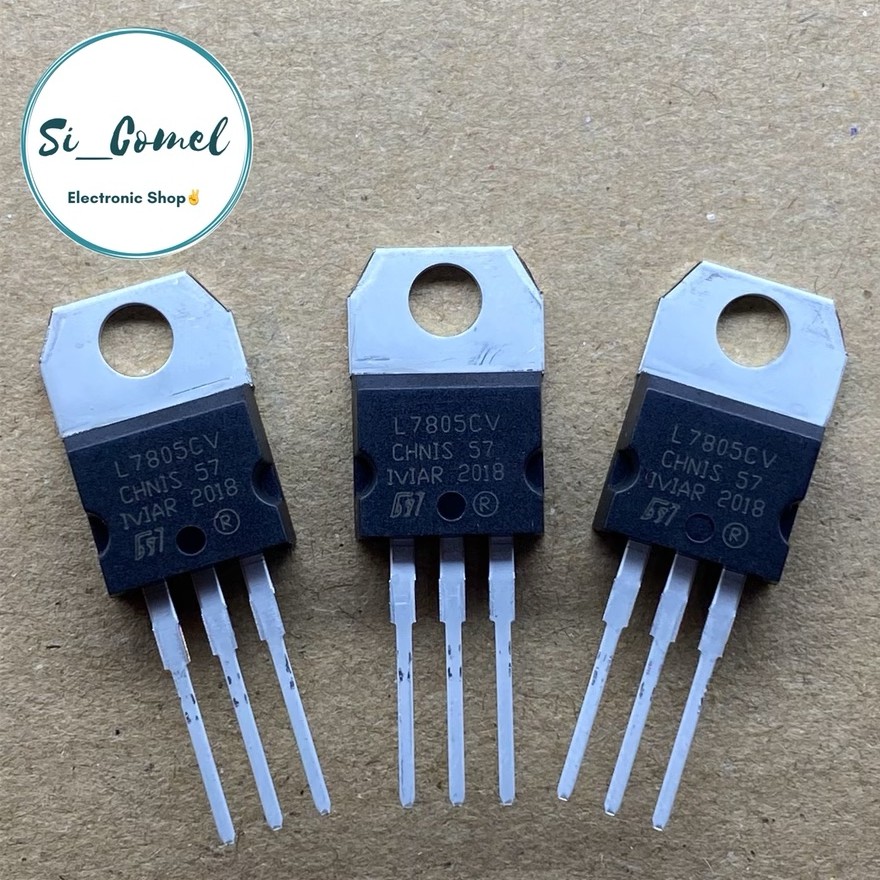
Info/Cost is RM 0.50 - Fake or real.jpeg
