kholia/HF-PA-v4/Wider-LPF/F1-Results.png

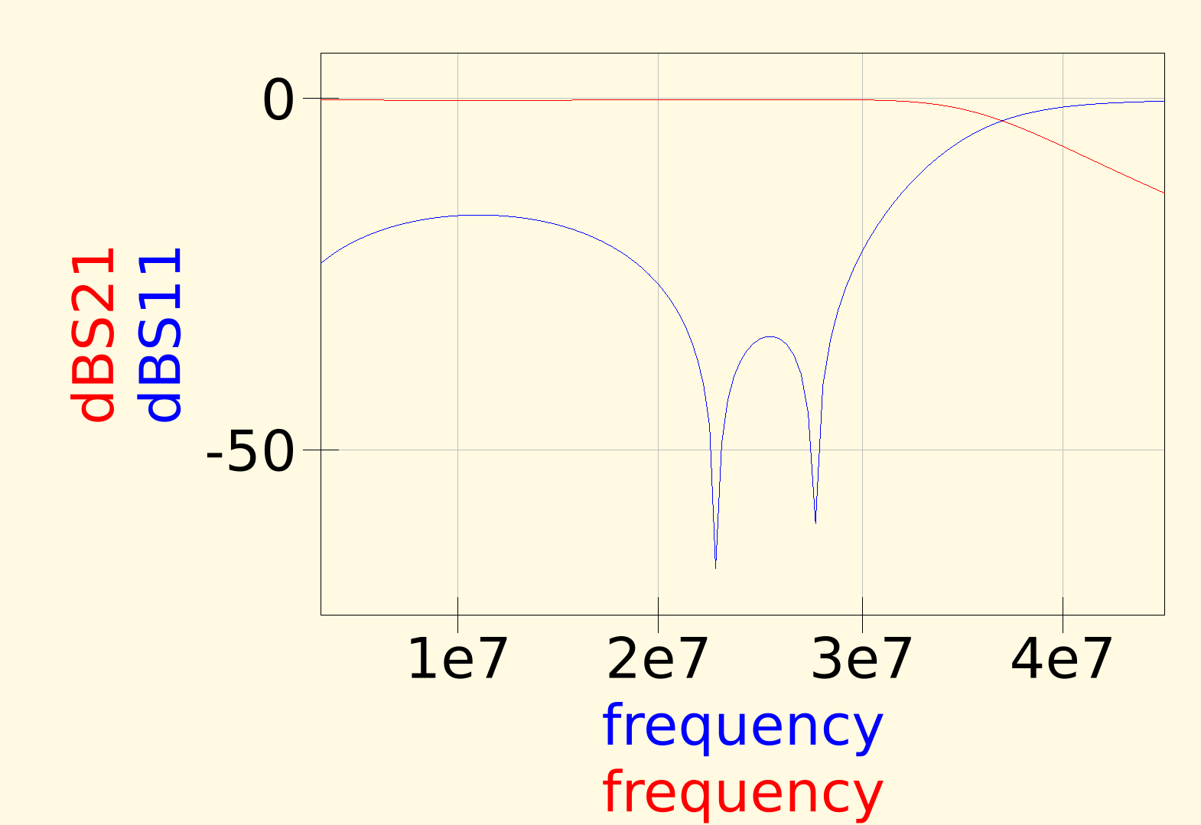
Wider-LPF/F1-Results.png
