kholia/HF-PA-v4/Wider-LPF/F2-Results.png

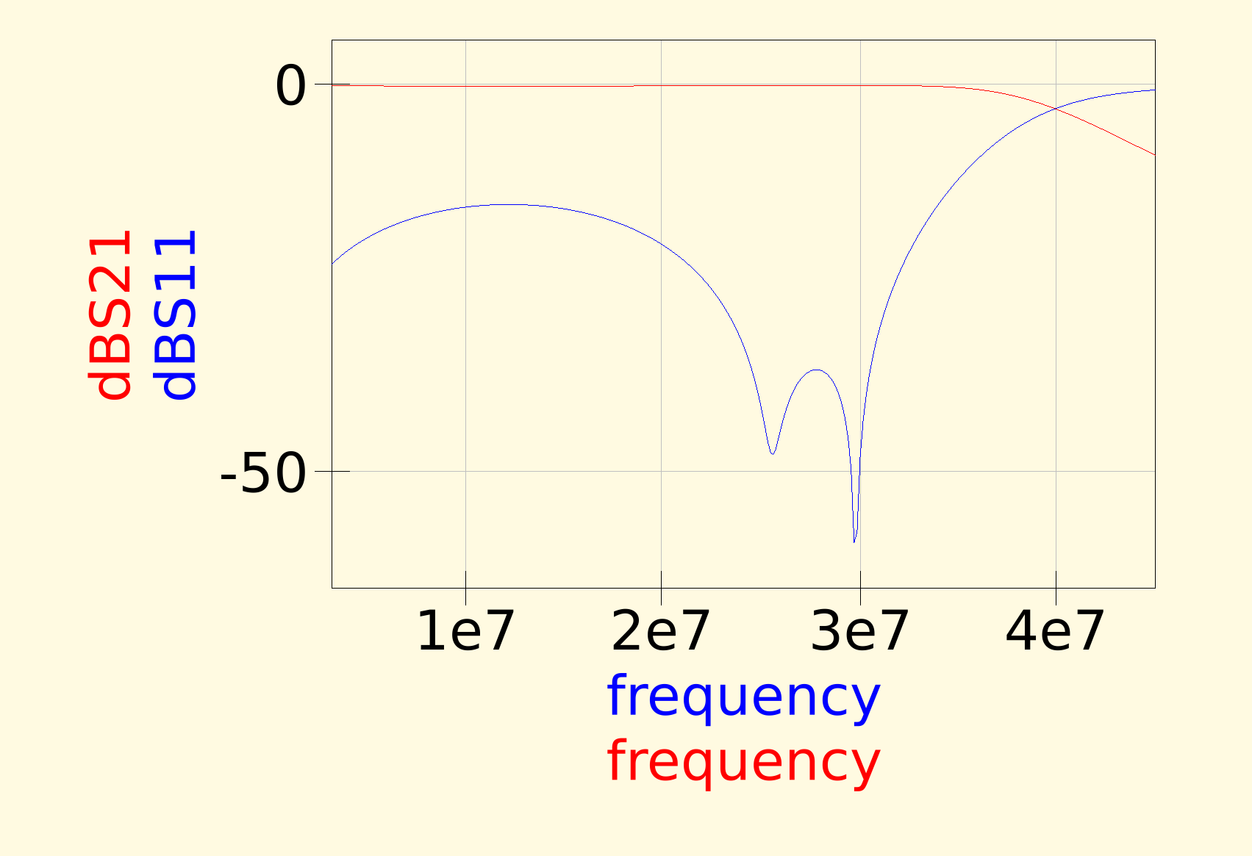
Wider-LPF/F2-Results.png
