kholia/HF-PA-v4/Wider-LPF/LPF-Simulation-Results.png

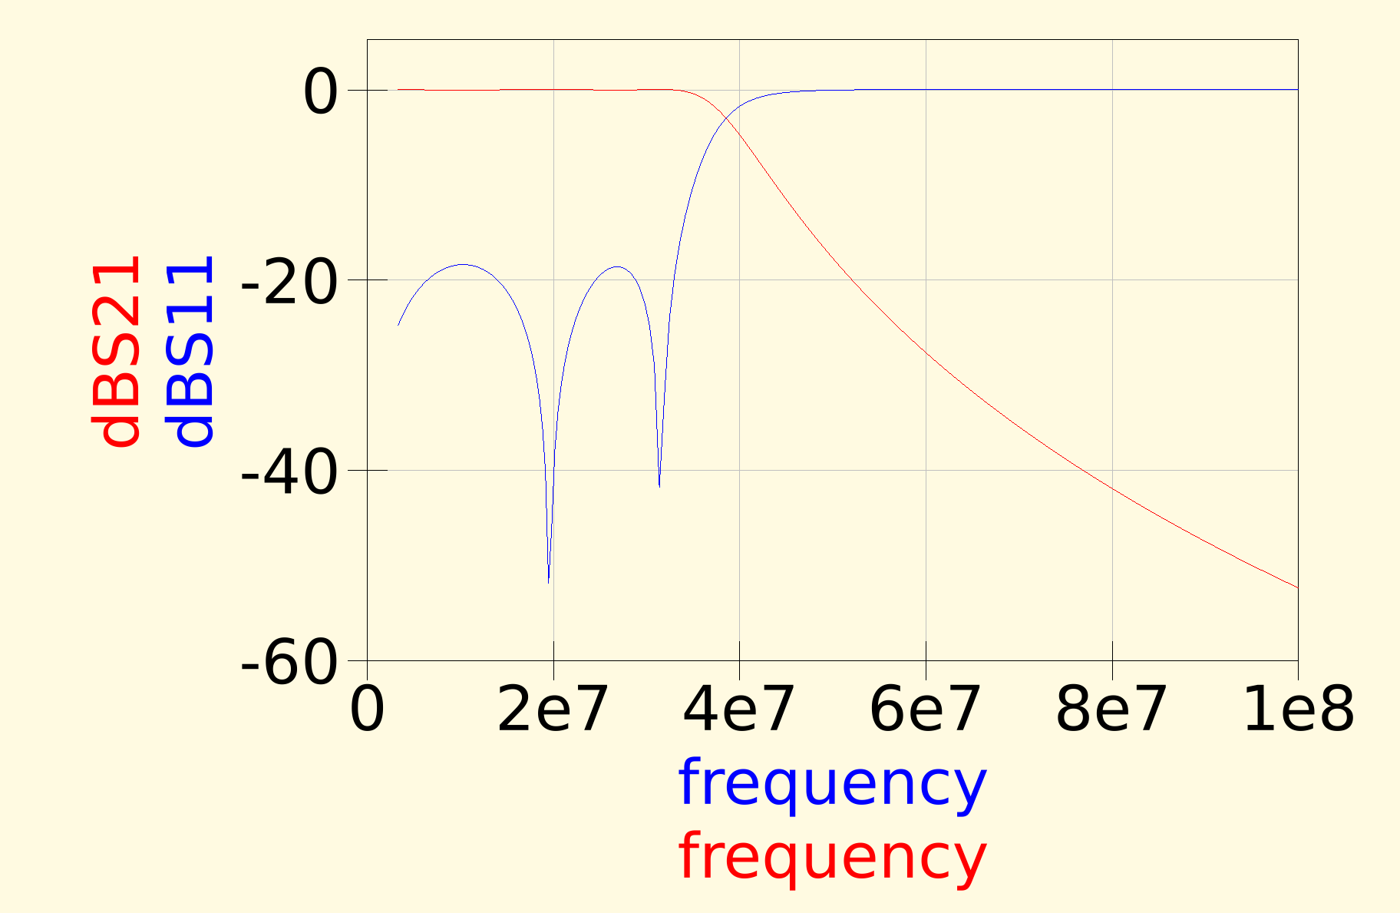
Wider-LPF/LPF-Simulation-Results.png
