kholia/HF-PA-v4/Wider-LPF/Validation - Screenshot_2021-10-15_14-24-16.png

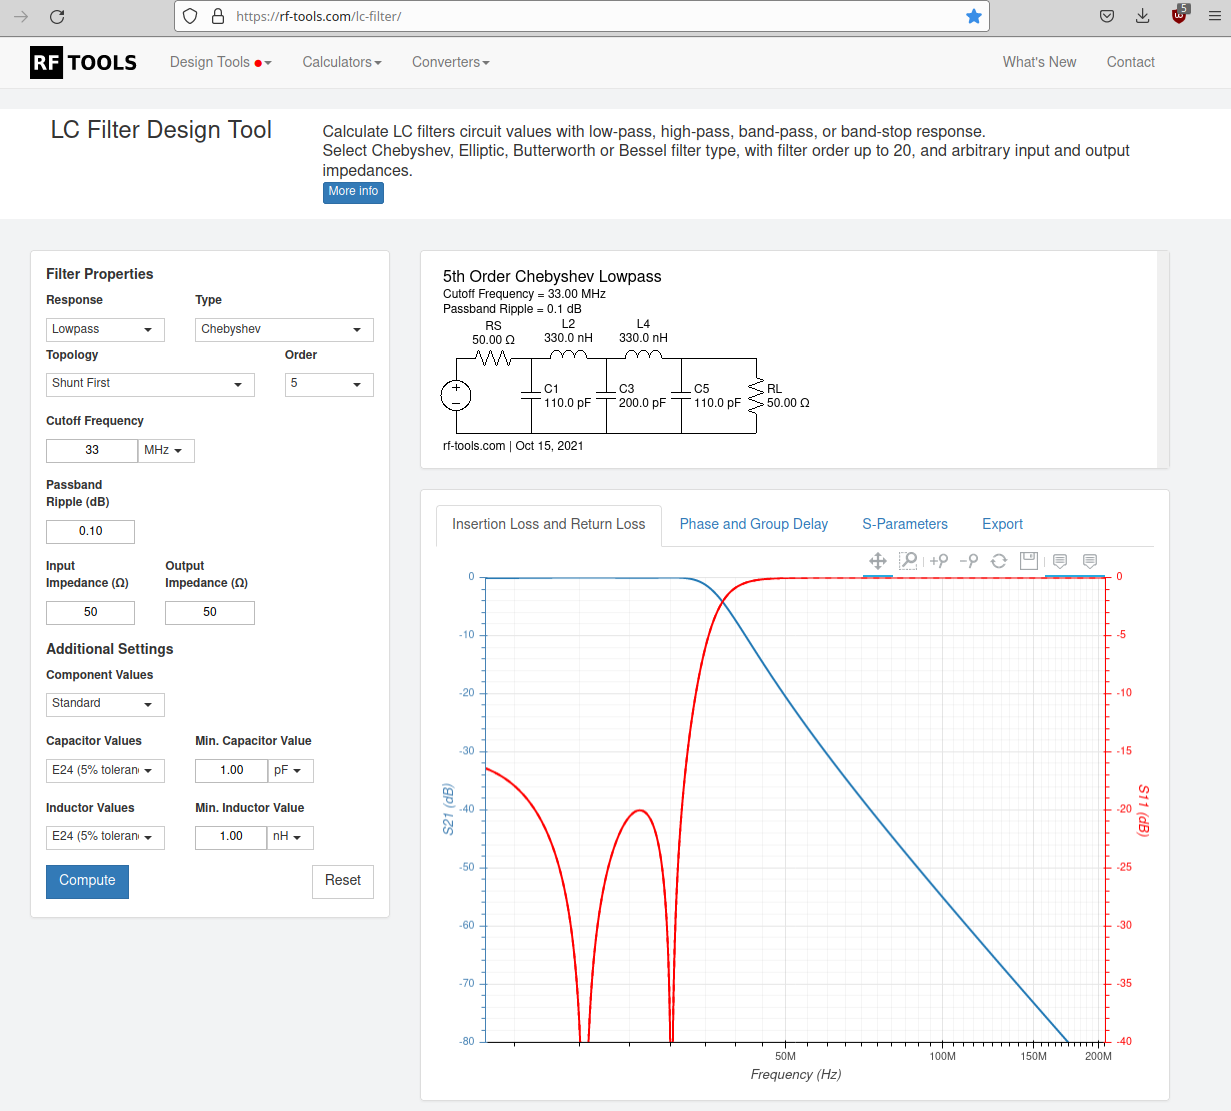
Wider-LPF/Validation - Screenshot_2021-10-15_14-24-16.png
