kholia/HF-PA-v4/Info/WSPR_RD16H_5W-PA_Sch_VK3PE_UPDATED.pdf

## 30M LPF

BN43-202

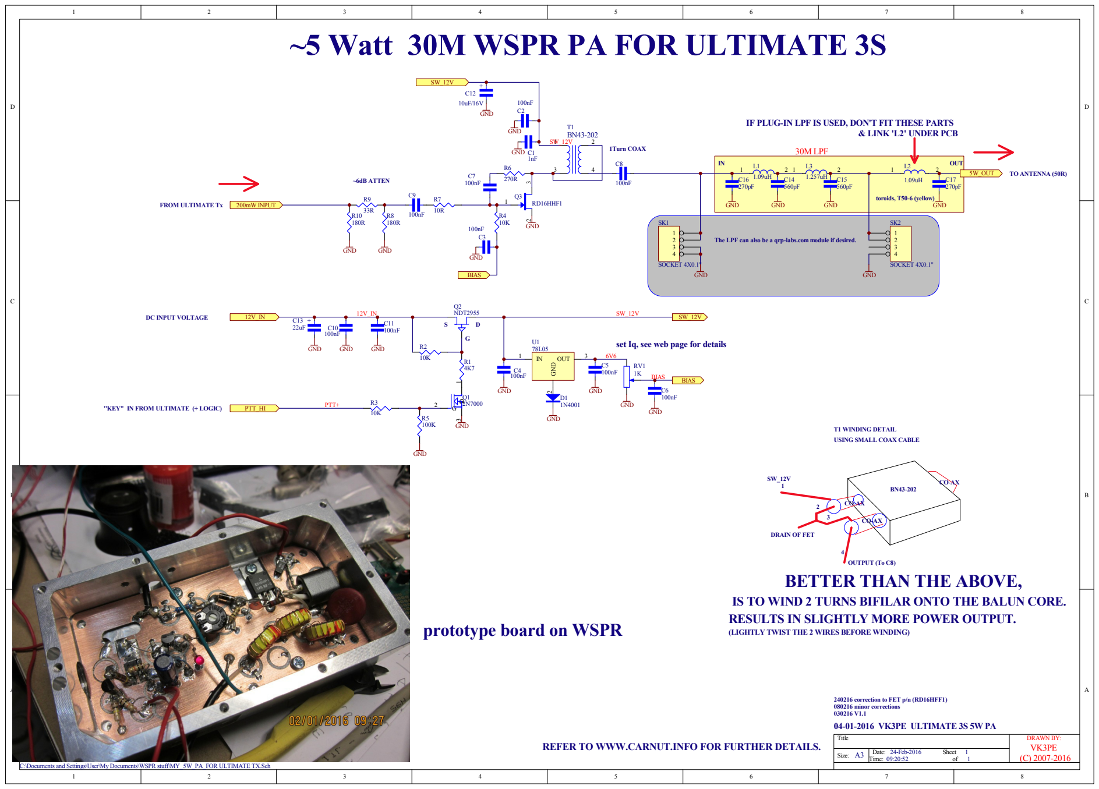
[picture p196: page 1]

~5 Watt 30M WSPR PA FOR ULTIMATE 3S

IF PLUG-IN LPF IS USED, DON'T FIT THESE PARTS

The LPF can also be a qrp-labs.com module if desired.

set Iq, see web page for details

''KEY" IN FROM ULTIMATE (+ LOGIC)

USING SMALL COAX CABLE

BETTER THAN THE ABOVE,

IS TO WIND 2 TURNS BIFILAR ONTO THE BALUN CORE.
RESULTS IN SLIGHTLY MORE POWER OUTPUT.

prototype board on WSPR

(LIGHTLY TWIST THE 2 WIRES BEFORE WINDING)

REFER TO WWW.CARNUT.INFO FOR FURTHER DETAILS.

C:\Documents and Settings\User\My Documents\WSPR stuff\MY_5W_PA_FOR ULTIMATE TX.Sch
